Safecast/bGeigieNanoKit/hardware/bGeigieNanoKit v1.0r4/bGeigieNanoKit v1.0r4_board.png

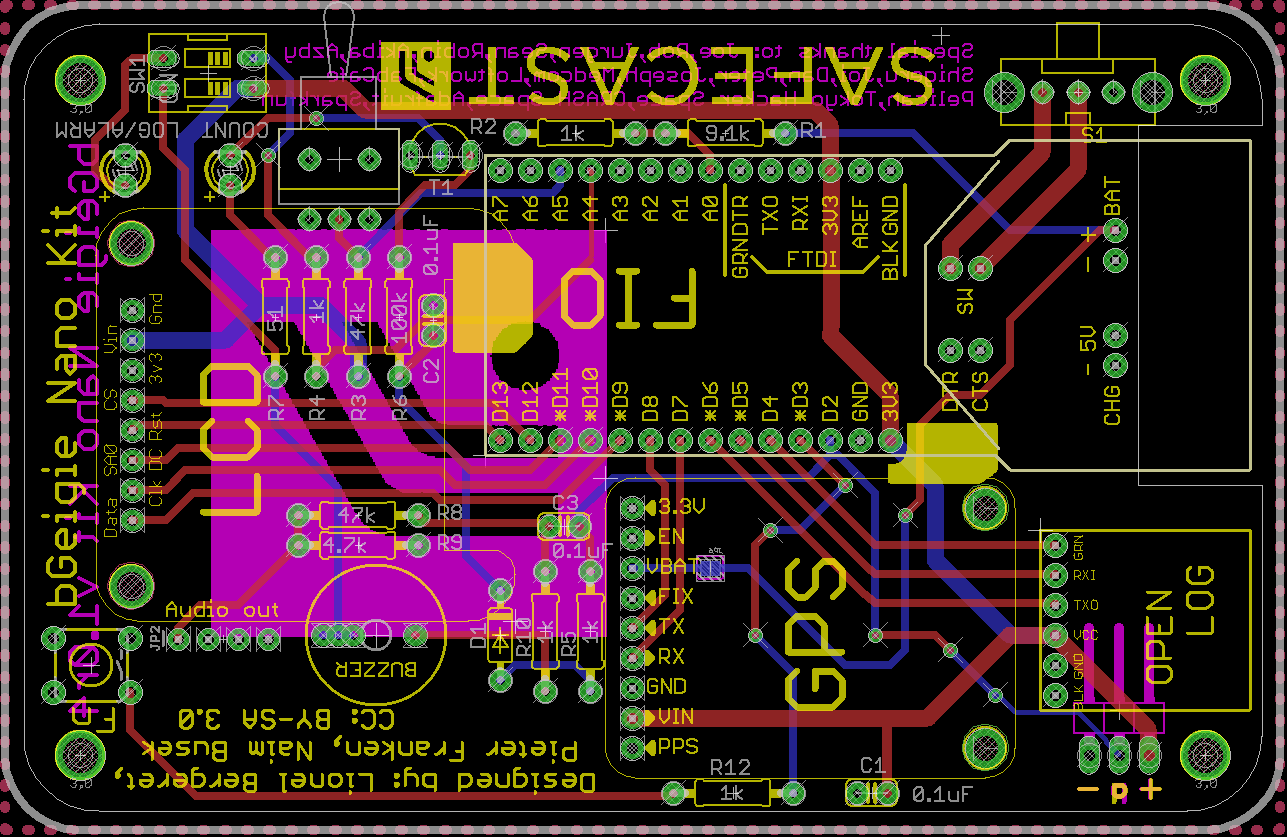
hardware/bGeigieNanoKit v1.0r4/bGeigieNanoKit v1.0r4_board.png
