Safecast/bGeigieNanoKit/hardware/bGeigieNanoKit V1.1r5/2017-06-08_bGeigieNanoKit V1.1r5x/bGeigieNano_V1.15x_board.jpg

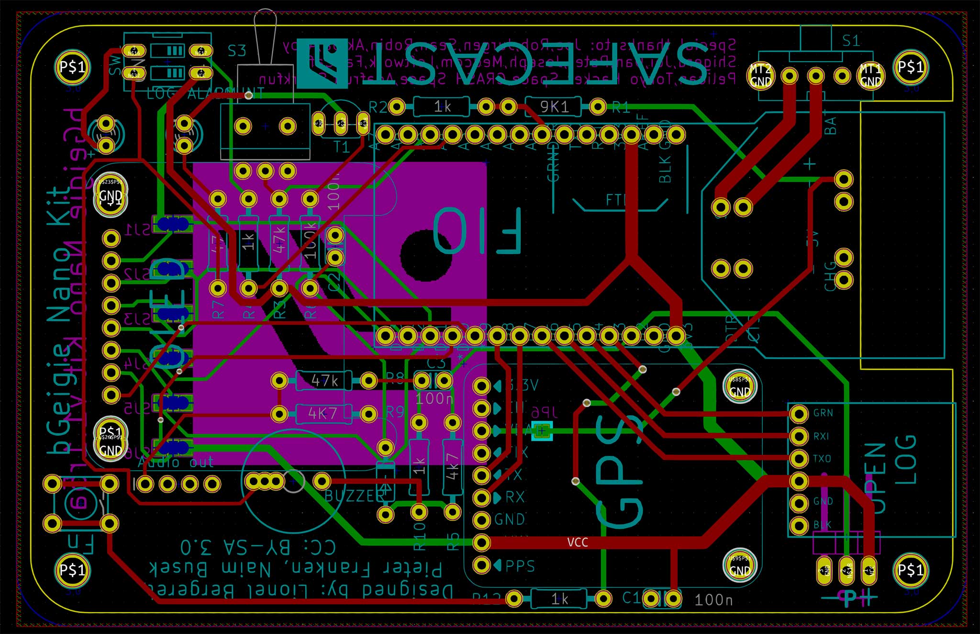
hardware/bGeigieNanoKit V1.1r5/2017-06-08_bGeigieNanoKit V1.1r5x/bGeigieNano_V1.15x_board.jpg
