Safecast/bGeigieNanoKit/hardware/bGeigieNanoKit/board_v1.1r4x.png

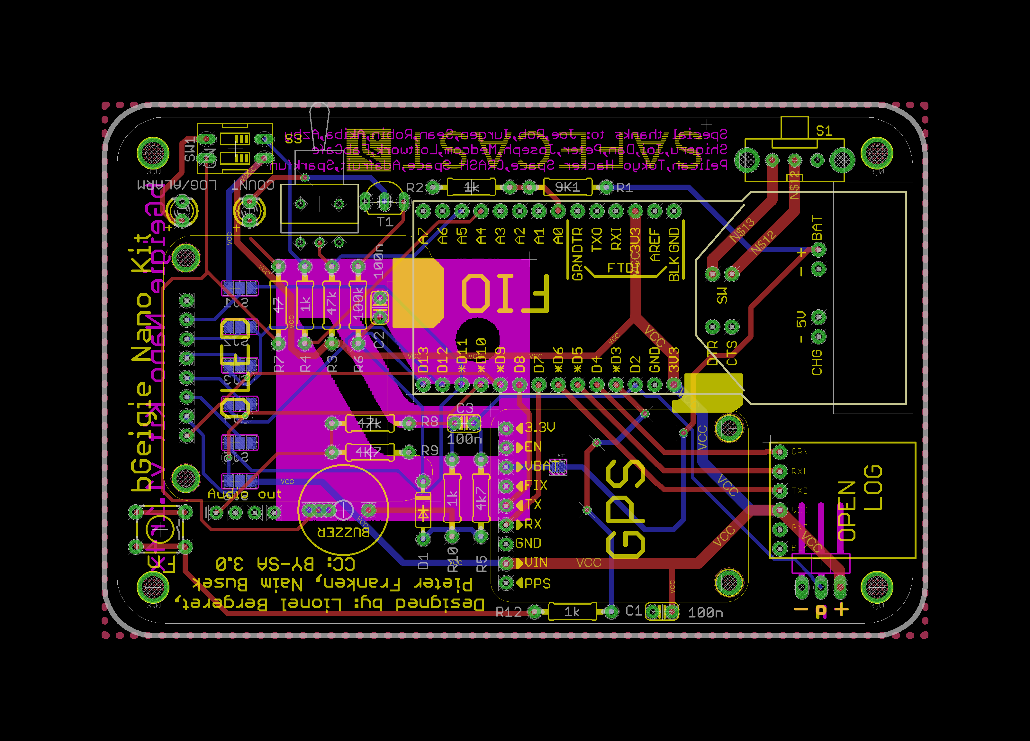
hardware/bGeigieNanoKit/board_v1.1r4x.png
