Safecast/bGeigieNanoKit/hardware/bGeigieNanoKit/S2660001.JPG

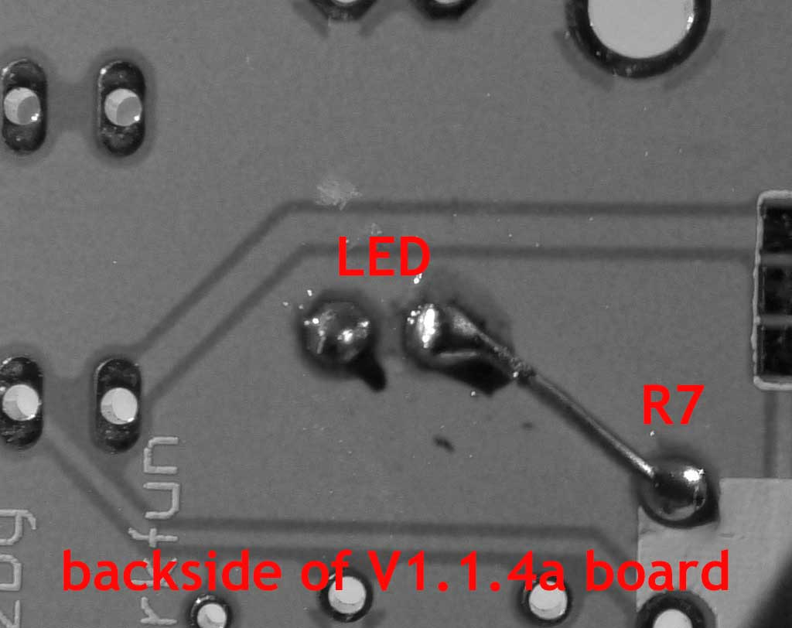
hardware/bGeigieNanoKit/S2660001.JPG
