Safecast/bGeigieNanoKit/nano manual named pics/manual update Aug 2018 small JPEG selects/078 wiki_small_components_31000px.jpg

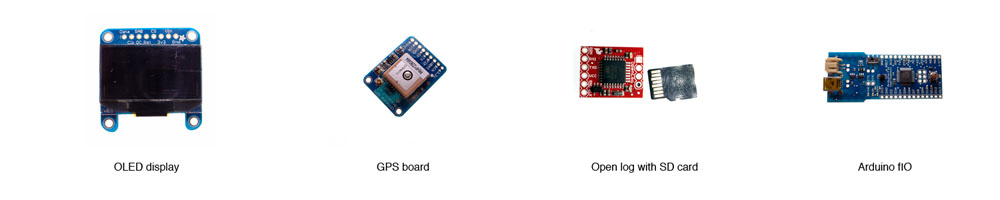
nano manual named pics/manual update Aug 2018 small JPEG selects/078 wiki_small_components_31000px.jpg
