Safecast/bGeigieNanoKit/nano manual named pics/manual update Aug 2018 small JPEG selects/_020-SmallComponentsIn-1000px[new].jpg

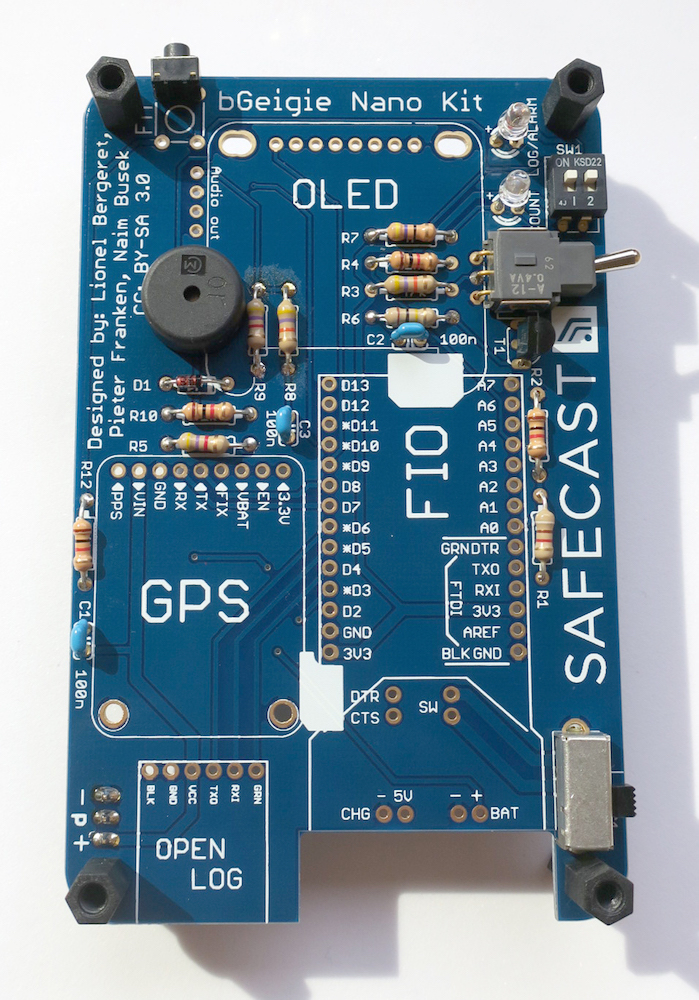
nano manual named pics/manual update Aug 2018 small JPEG selects/_020-SmallComponentsIn-1000px[new].jpg
