Safecast/bGeigieNanoKit/nano manual named pics/manual update Aug 2018 small JPEG selects/v1.0r3_placement guide large parts.jpg

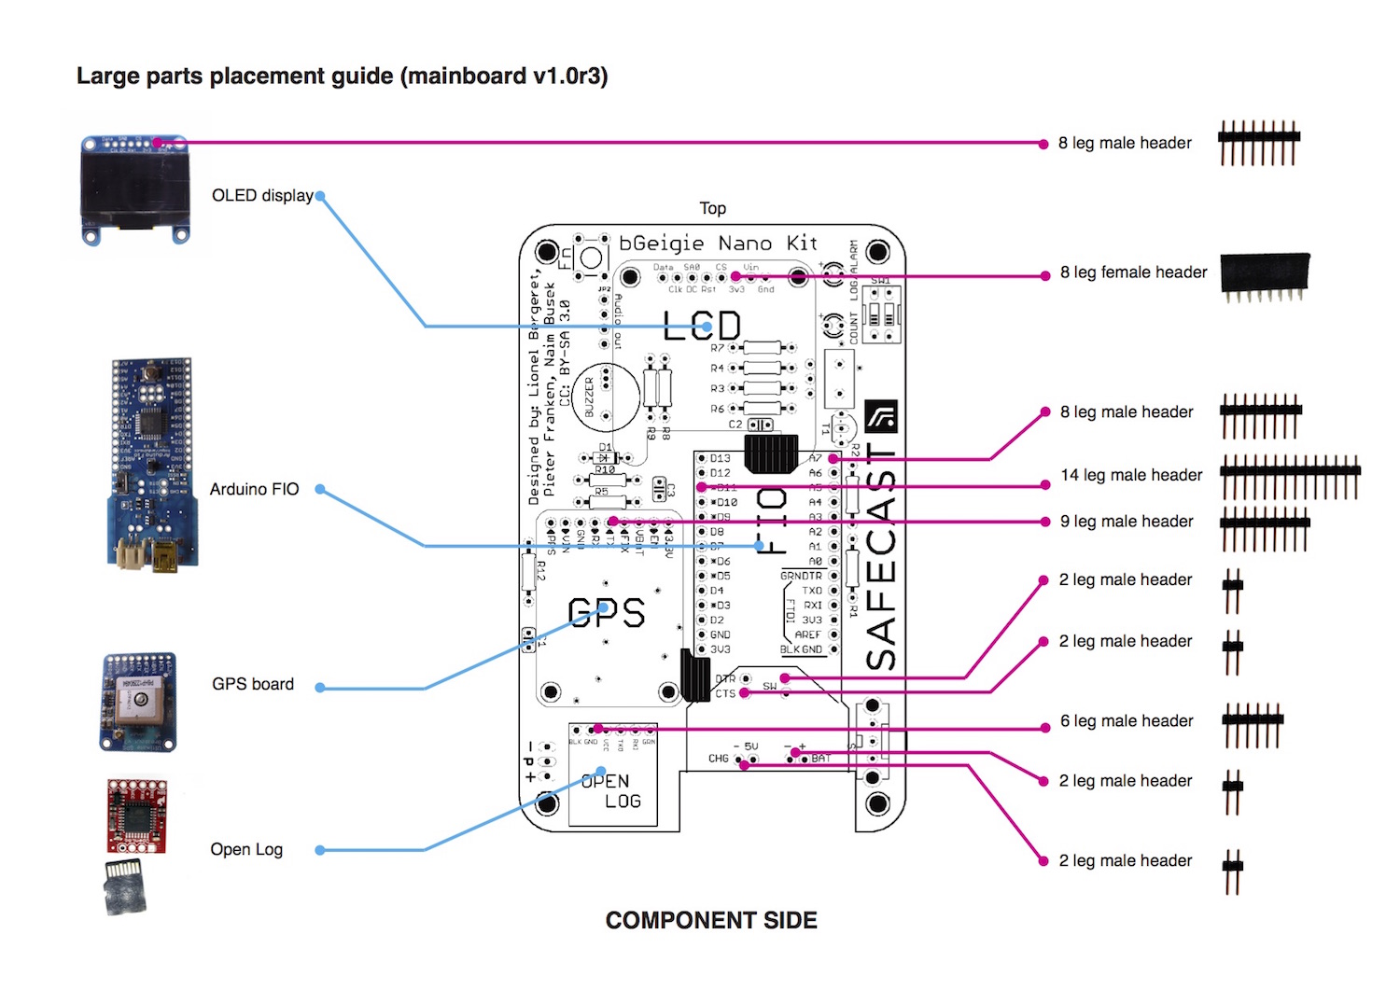
nano manual named pics/manual update Aug 2018 small JPEG selects/v1.0r3_placement guide large parts.jpg
