Safecast/bGeigieNanoKit/nano manual named pics/wiki_small_components_2.jpg

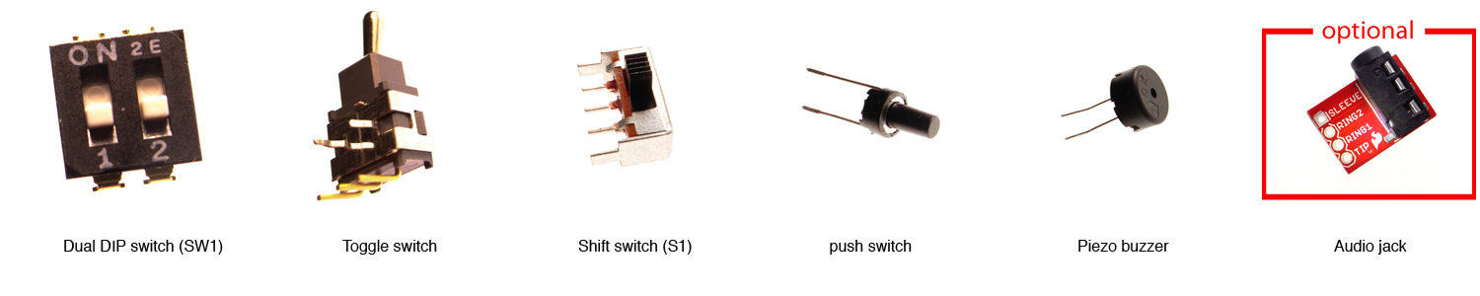
nano manual named pics/wiki_small_components_2.jpg
