Safecast/bGeigieNanoKit/nano manual named pics/wiki_small_components_4.jpg

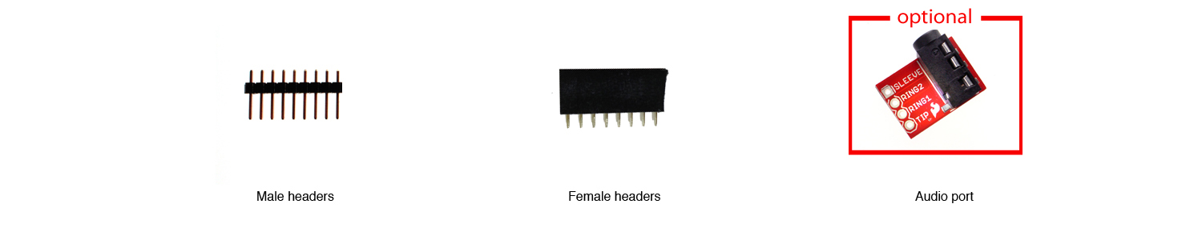
nano manual named pics/wiki_small_components_4.jpg
