Safecast/bGeigieNanoKit/assembly/bGeigieNanoKit_bb.png

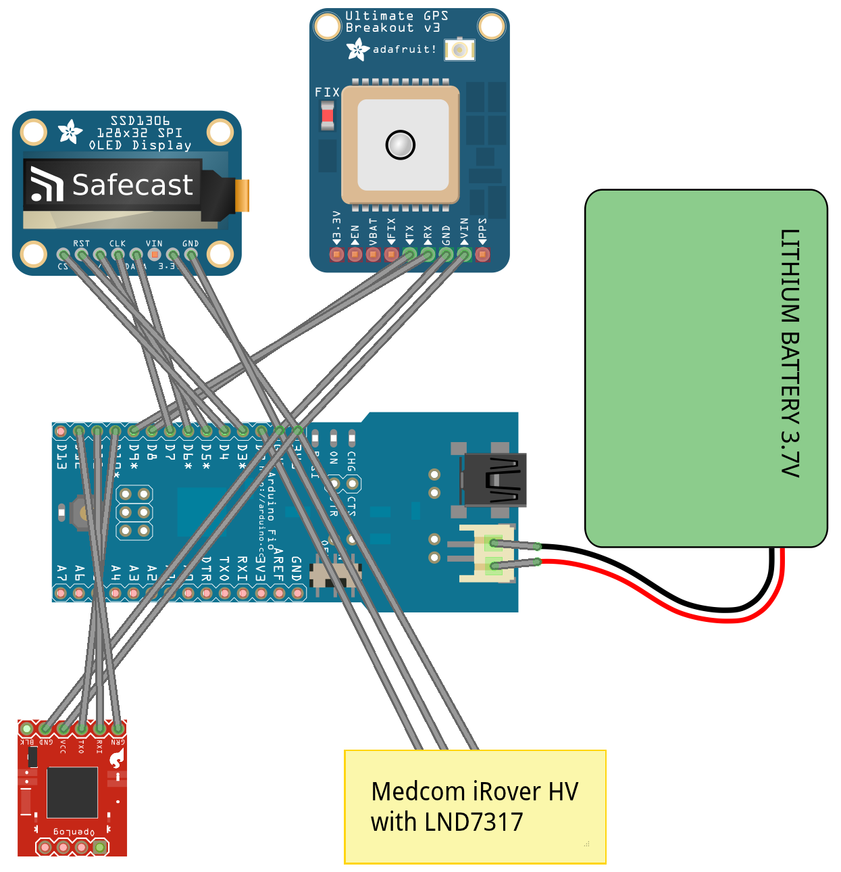
assembly/bGeigieNanoKit_bb.png
