Safecast/bGeigieNanoKit/assembly/bGeigieNanoKit_sheet.png

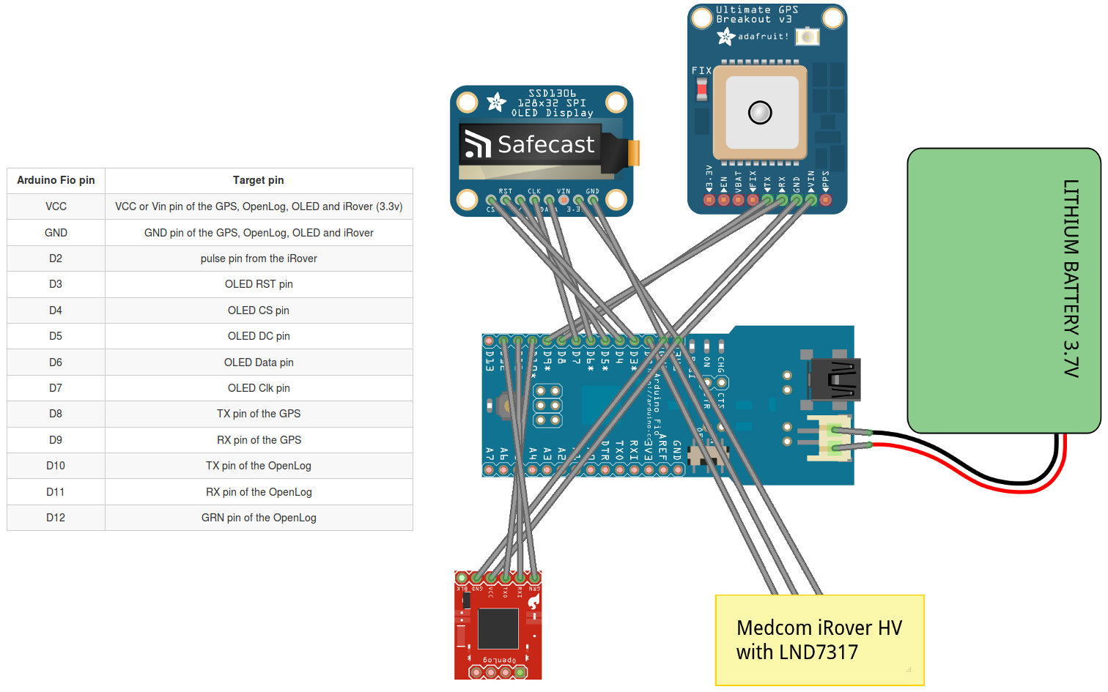
assembly/bGeigieNanoKit_sheet.png
