Safecast/bGeigieNanoKit/nano manual named pics/assembly.jpg

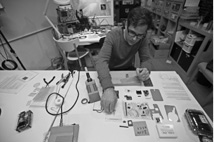
nano manual named pics/assembly.jpg
