Safecast/bGeigieNanoKit/nano manual named pics/attaching_iRover.jpg

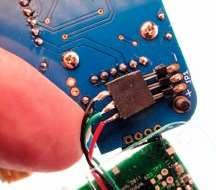
nano manual named pics/attaching_iRover.jpg
