Safecast/bGeigieNanoKit/nano manual named pics/attaching_sensor_to_iRover.jpg

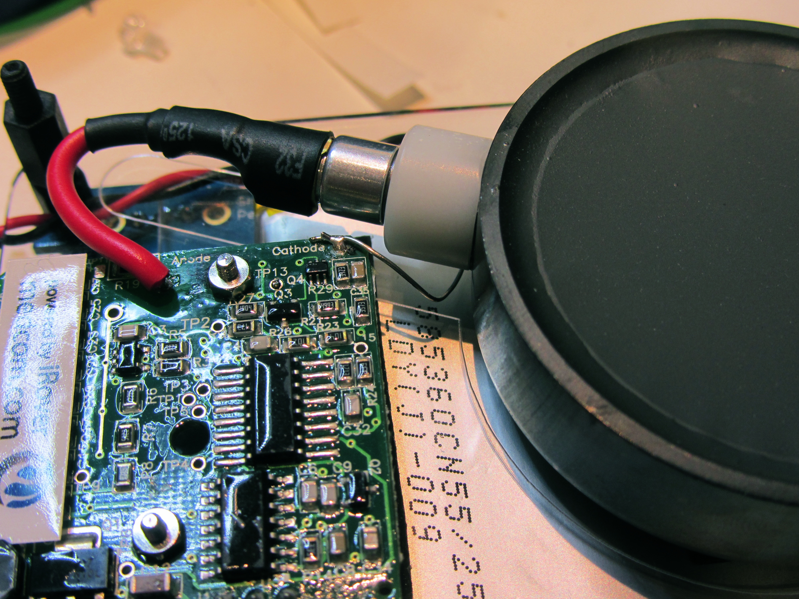
nano manual named pics/attaching_sensor_to_iRover.jpg
