Safecast/bGeigieNanoKit/nano manual named pics/back_headers_top.jpg

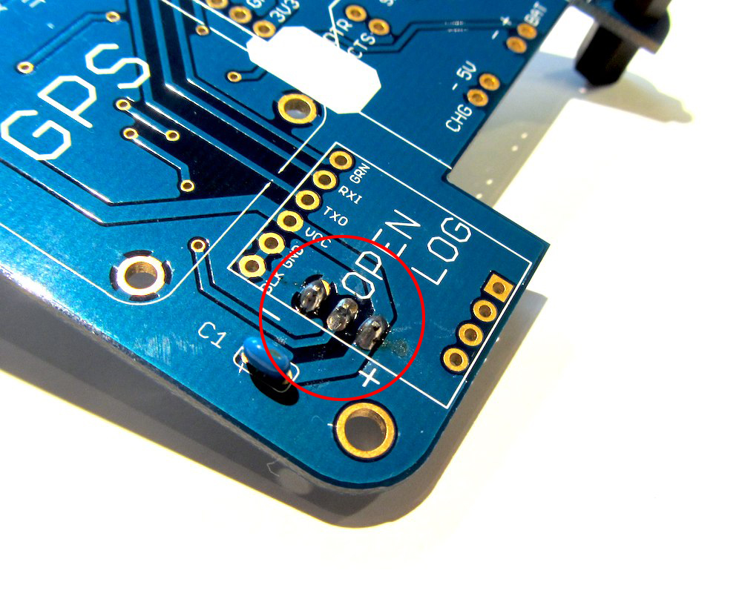
nano manual named pics/back_headers_top.jpg
