Safecast/bGeigieNanoKit/nano manual named pics/back_plate_install.jpg

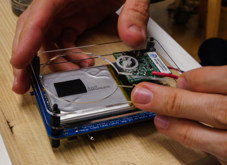
nano manual named pics/back_plate_install.jpg
