Safecast/bGeigieNanoKit/nano manual named pics/battery-compo01.jpg

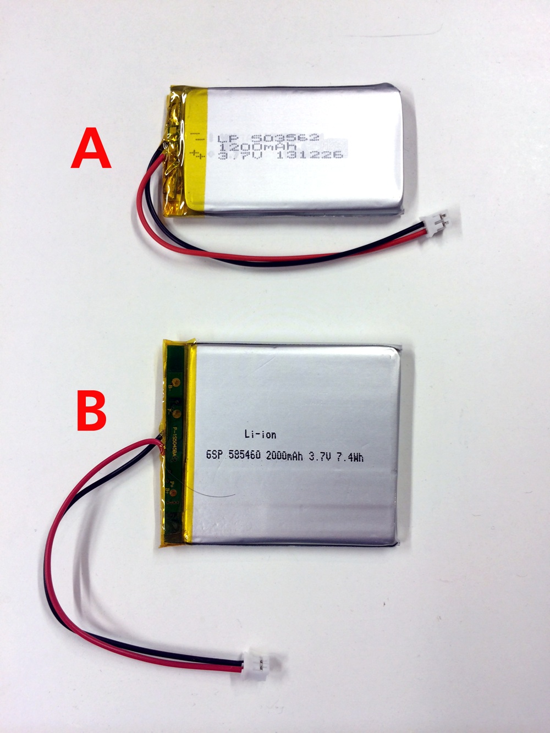
nano manual named pics/battery-compo01.jpg
