Safecast/bGeigieNanoKit/nano manual named pics/battery_location.jpg

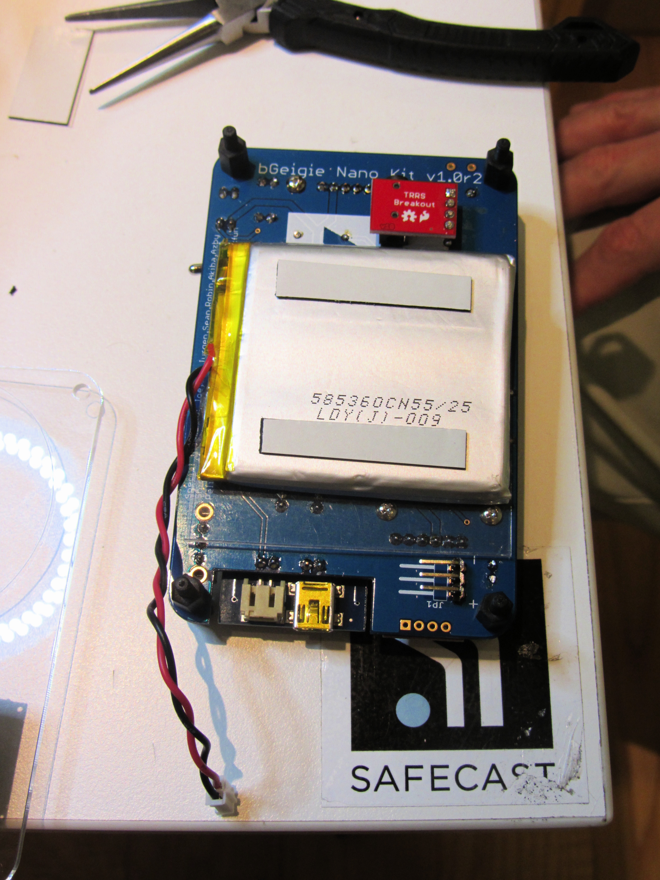
nano manual named pics/battery_location.jpg
