Safecast/bGeigieNanoKit/nano manual named pics/beercantrick.jpg

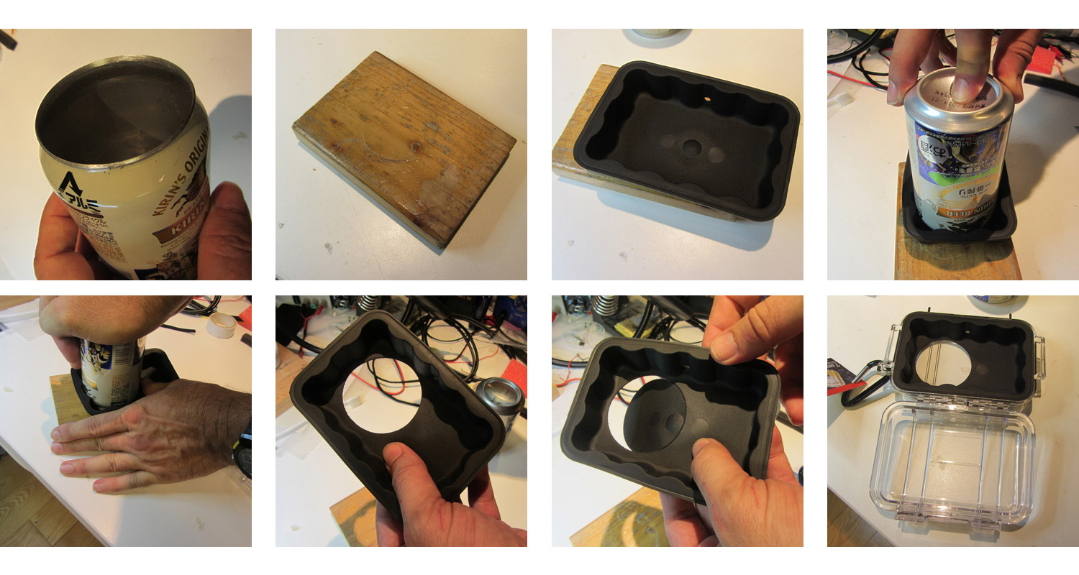
nano manual named pics/beercantrick.jpg
