Safecast/bGeigieNanoKit/nano manual named pics/bGeigie_Nano_bottom.jpg

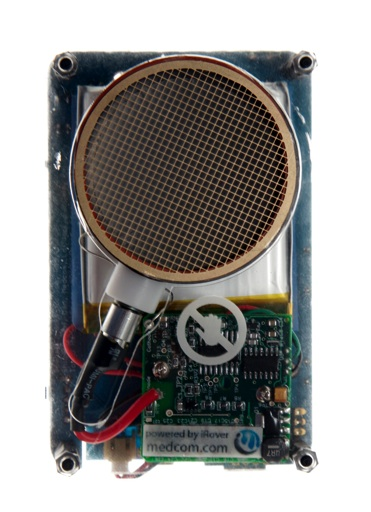
nano manual named pics/bGeigie_Nano_bottom.jpg
