Safecast/bGeigieNanoKit/nano manual named pics/bGeigie_Nano_side2.jpg

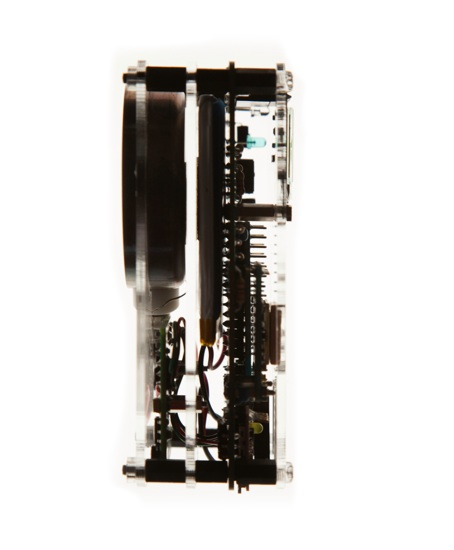
nano manual named pics/bGeigie_Nano_side2.jpg
