Safecast/bGeigieNanoKit/nano manual named pics/bGeigie_Nano_side.jpg

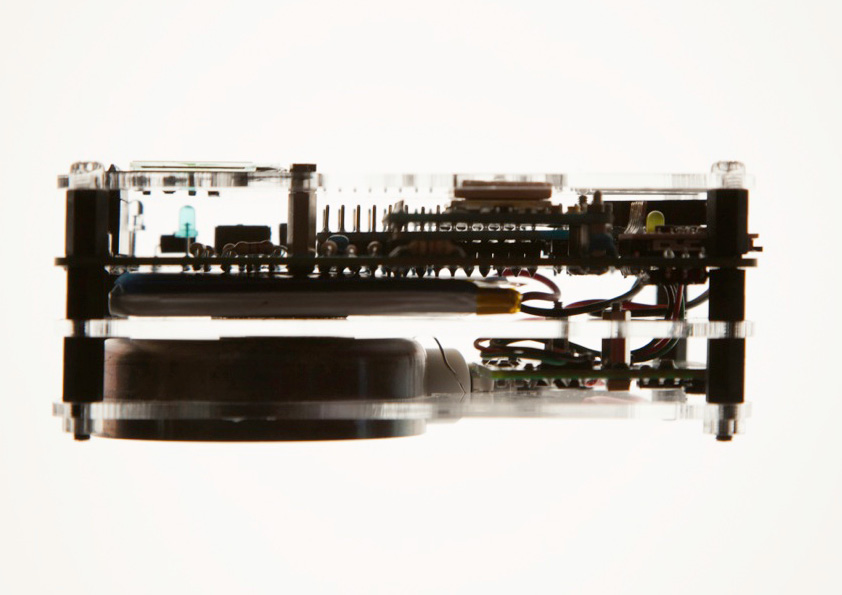
nano manual named pics/bGeigie_Nano_side.jpg
