Safecast/bGeigieNanoKit/nano manual named pics/broken_sensor.jpg

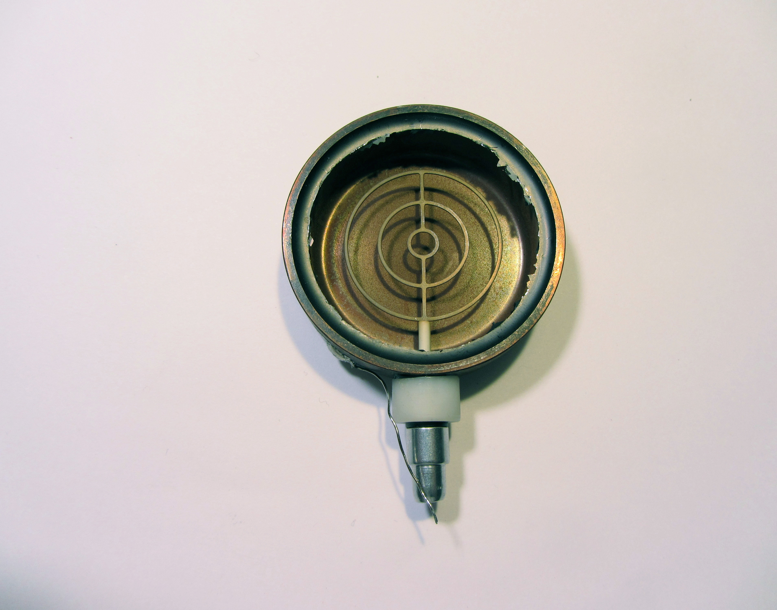
nano manual named pics/broken_sensor.jpg
