Safecast/bGeigieNanoKit/nano manual named pics/buttonguideNano.jpg

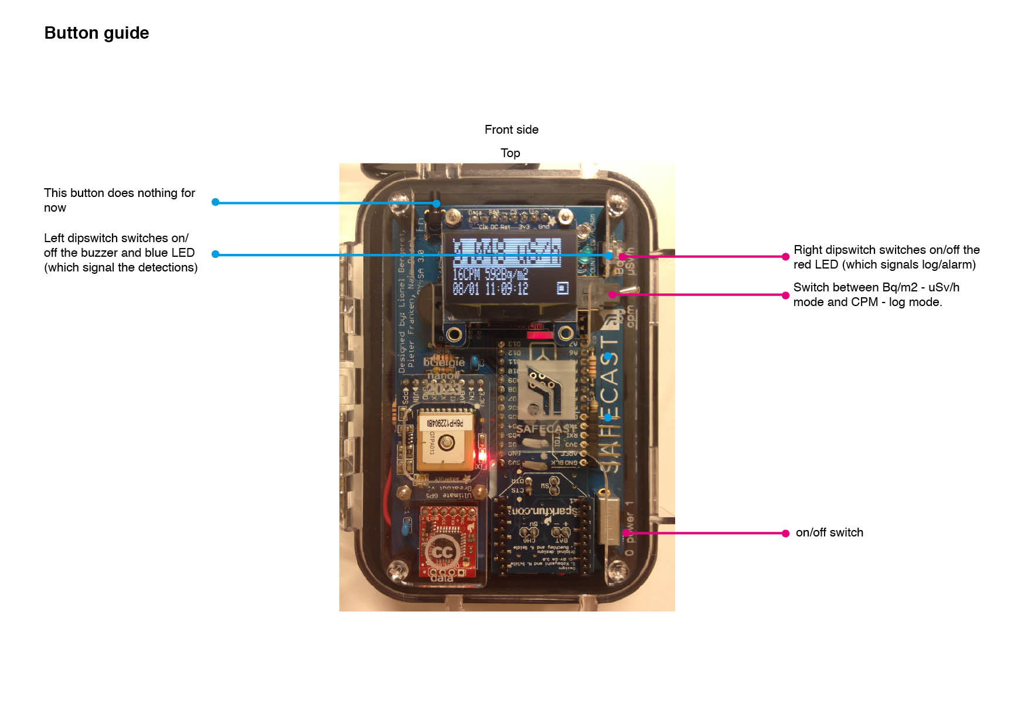
nano manual named pics/buttonguideNano.jpg
