Safecast/bGeigieNanoKit/nano manual named pics/closed_front.jpg

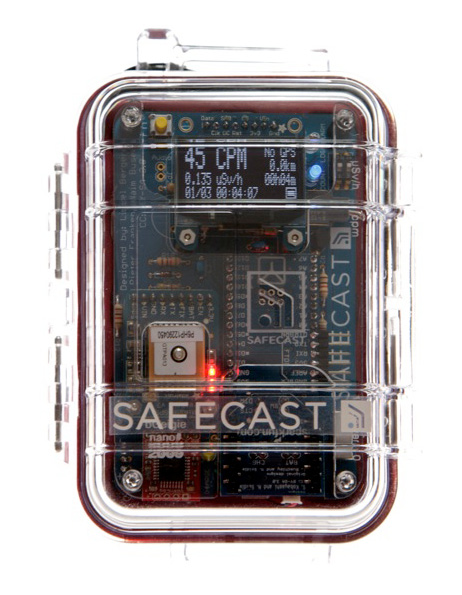
nano manual named pics/closed_front.jpg
