Safecast/bGeigieNanoKit/nano manual named pics/cutting_liner.jpg

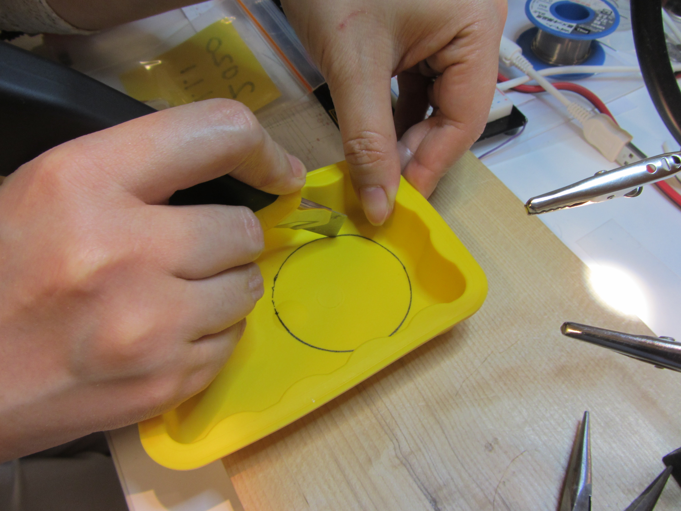
nano manual named pics/cutting_liner.jpg
