Safecast/bGeigieNanoKit/nano manual named pics/displayupdate/2020-new-display-cut-jumper.jpg

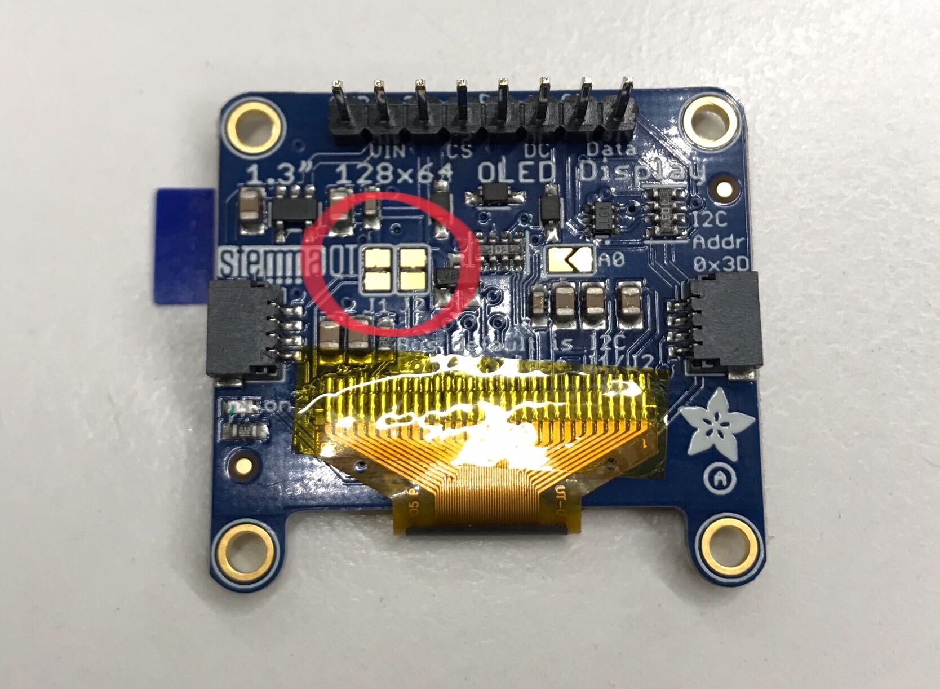
nano manual named pics/displayupdate/2020-new-display-cut-jumper.jpg
