Safecast/bGeigieNanoKit/nano manual named pics/displayupdate/2020-new-display-post-cut.jpg

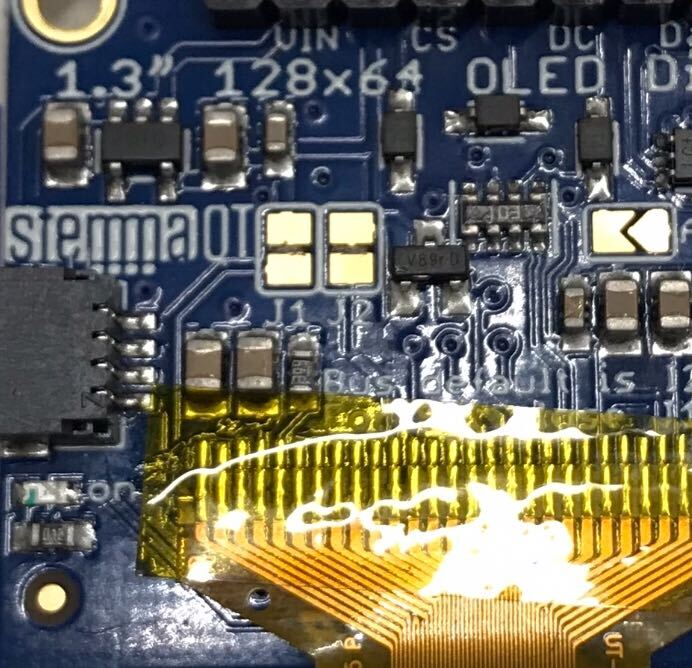
nano manual named pics/displayupdate/2020-new-display-post-cut.jpg
