Safecast/bGeigieNanoKit/nano manual named pics/displayupdate/2020-new-display-pre-cut.jpg

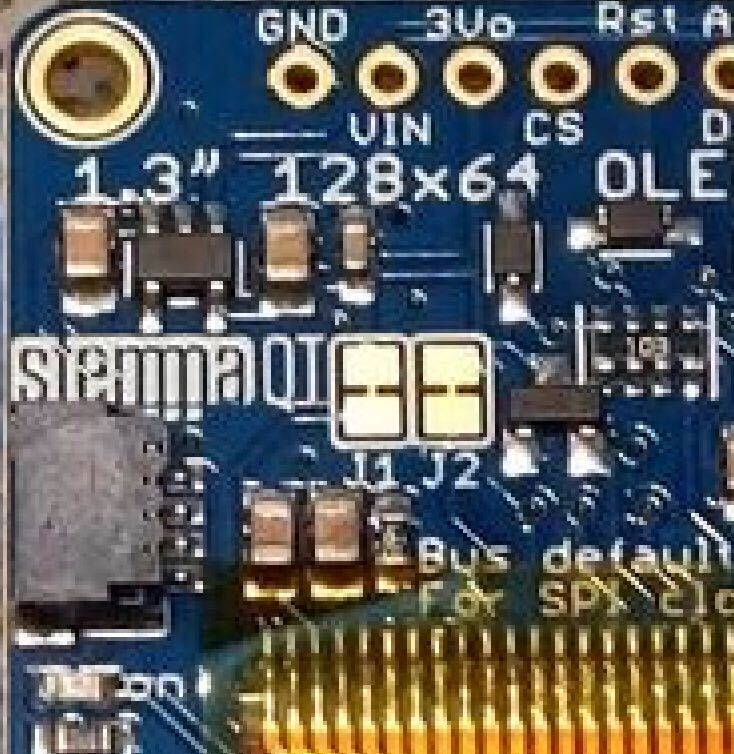
nano manual named pics/displayupdate/2020-new-display-pre-cut.jpg
