Safecast/bGeigieNanoKit/nano manual named pics/finished_assembly_top.jpg

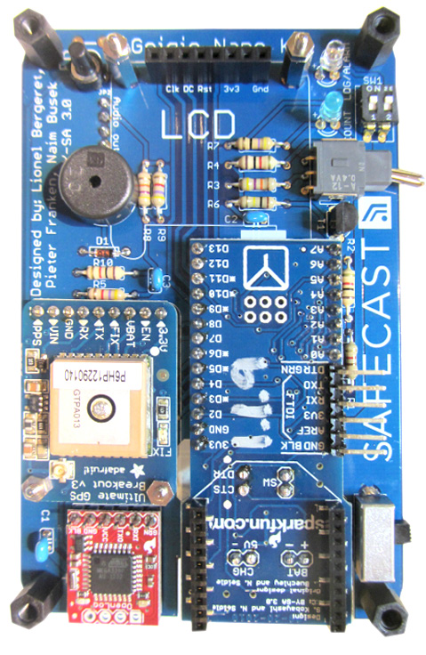
nano manual named pics/finished_assembly_top.jpg
