Safecast/bGeigieNanoKit/nano manual named pics/Fio_header_tip2.jpg

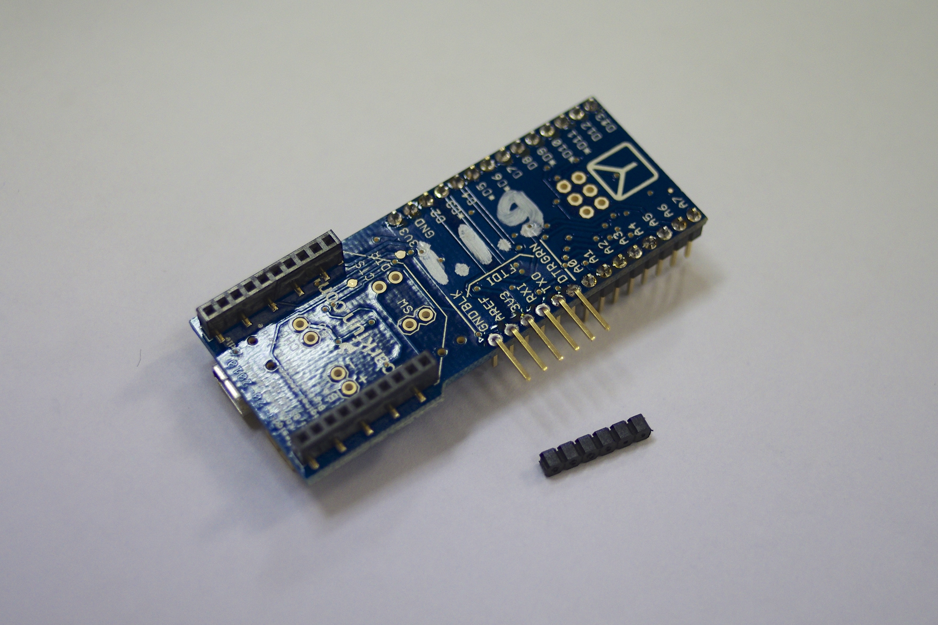
nano manual named pics/Fio_header_tip2.jpg
