Safecast/bGeigieNanoKit/nano manual named pics/Fio_header_tip.jpg

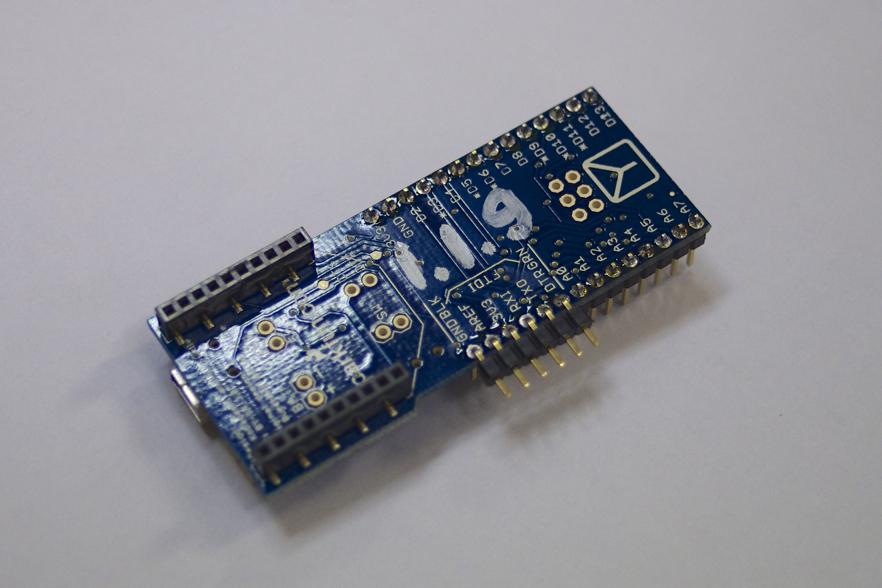
nano manual named pics/Fio_header_tip.jpg
