Safecast/bGeigieNanoKit/nano manual named pics/fio_placement.jpg

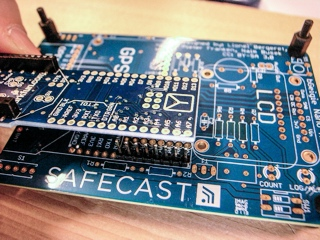
nano manual named pics/fio_placement.jpg
