Safecast/bGeigieNanoKit/nano manual named pics/fully_assembled_top.jpg

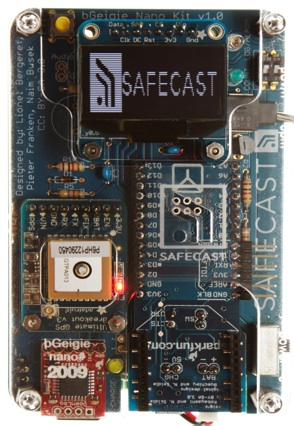
nano manual named pics/fully_assembled_top.jpg
