Safecast/bGeigieNanoKit/nano manual named pics/gps_placement.jpg

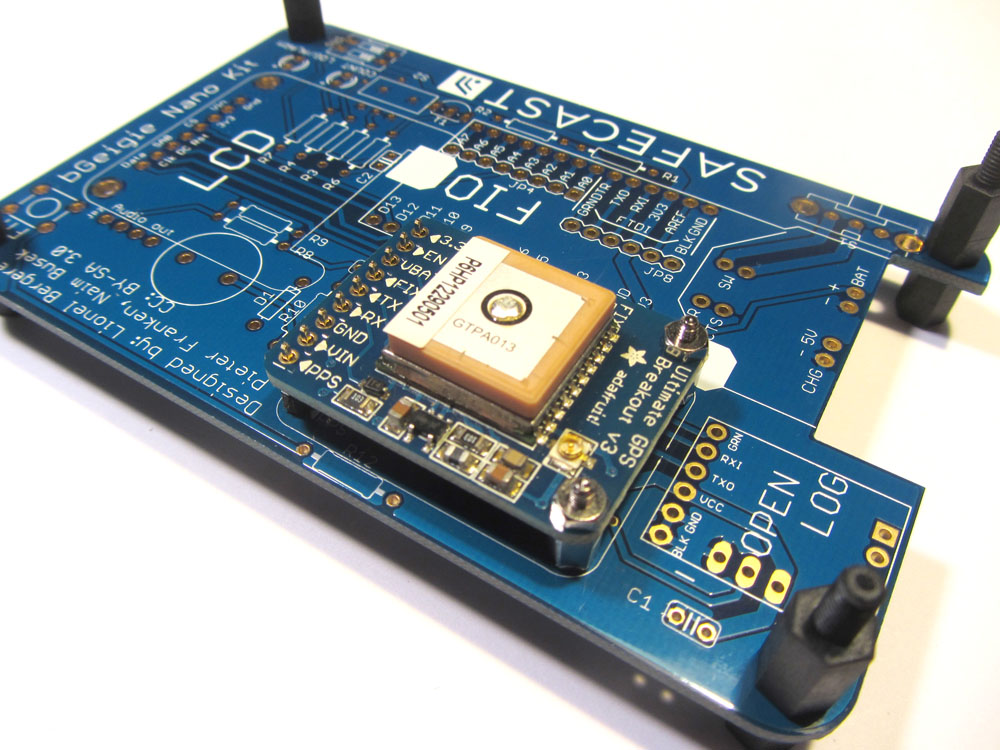
nano manual named pics/gps_placement.jpg
