Safecast/bGeigieNanoKit/nano manual named pics/iRover_attachment.jpg

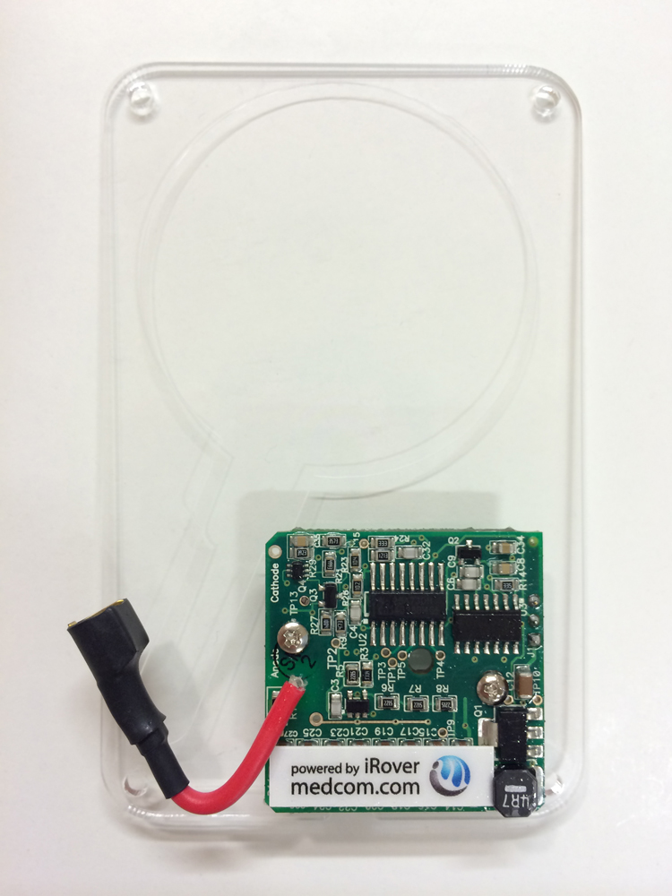
nano manual named pics/iRover_attachment.jpg
