Safecast/bGeigieNanoKit/nano manual named pics/iRover_header_tip2.jpg

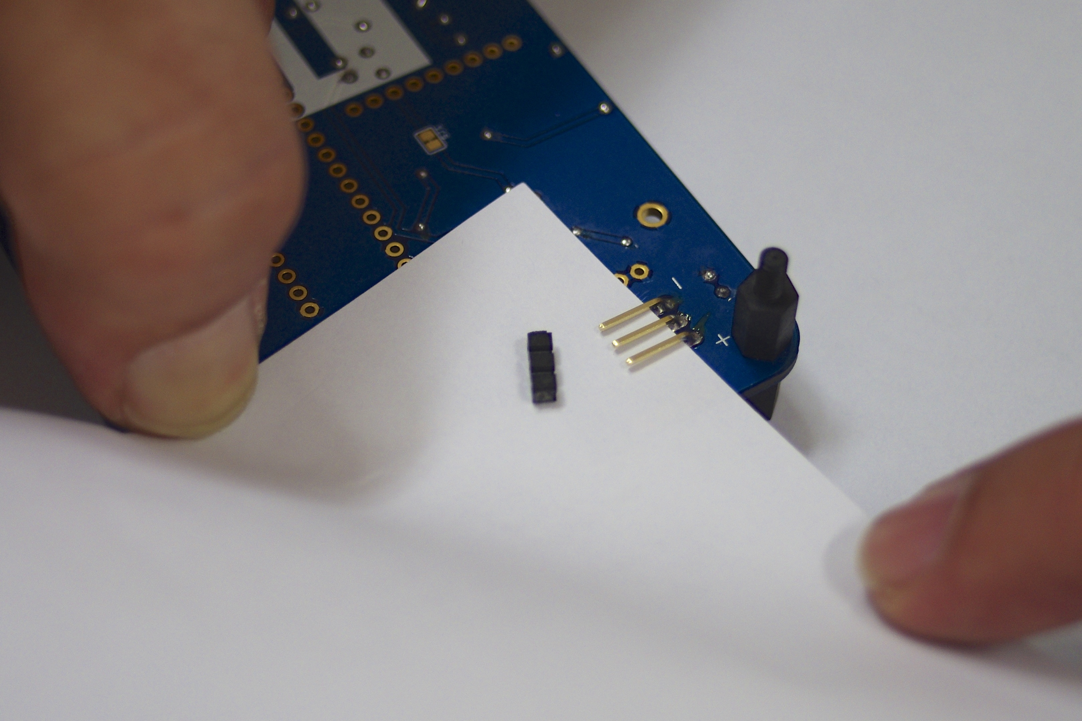
nano manual named pics/iRover_header_tip2.jpg
