Safecast/bGeigieNanoKit/nano manual named pics/iRover_headers.jpg

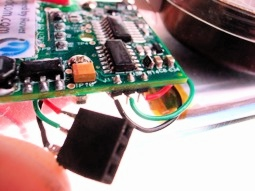
nano manual named pics/iRover_headers.jpg
