Safecast/bGeigieNanoKit/nano manual named pics/iRover_placement.jpg

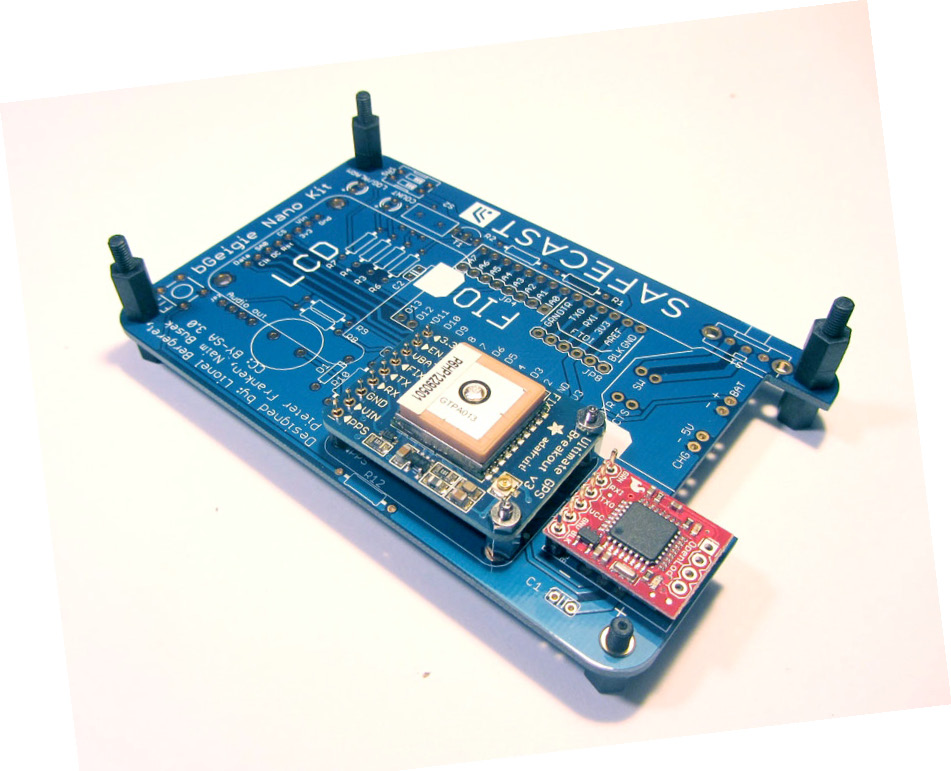
nano manual named pics/iRover_placement.jpg
