Safecast/bGeigieNanoKit/nano manual named pics/iRover_positioning.jpg

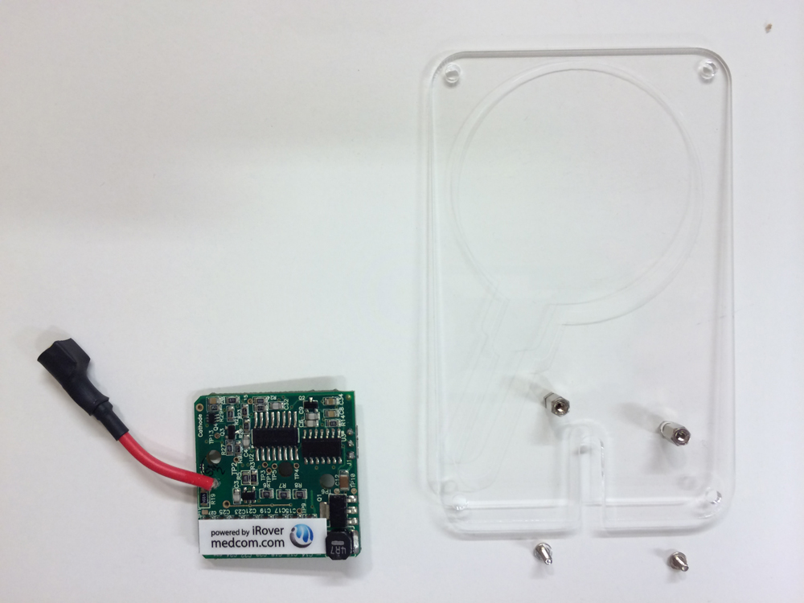
nano manual named pics/iRover_positioning.jpg
