Safecast/bGeigieNanoKit/nano manual named pics/iRover_wire_feedthrough.jpg

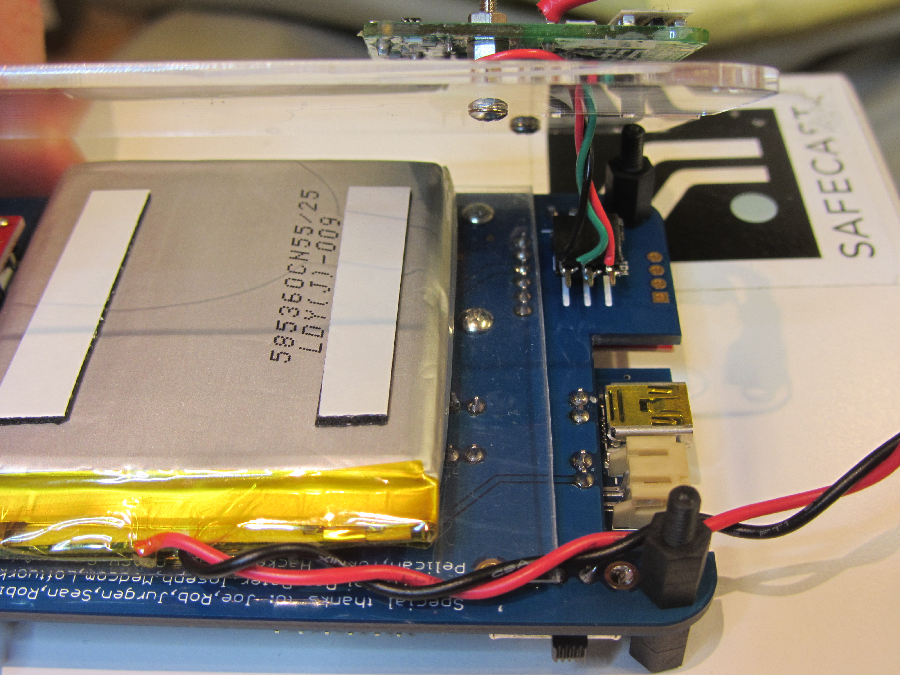
nano manual named pics/iRover_wire_feedthrough.jpg
