Safecast/bGeigieNanoKit/nano manual named pics/iRover_wiring.jpg

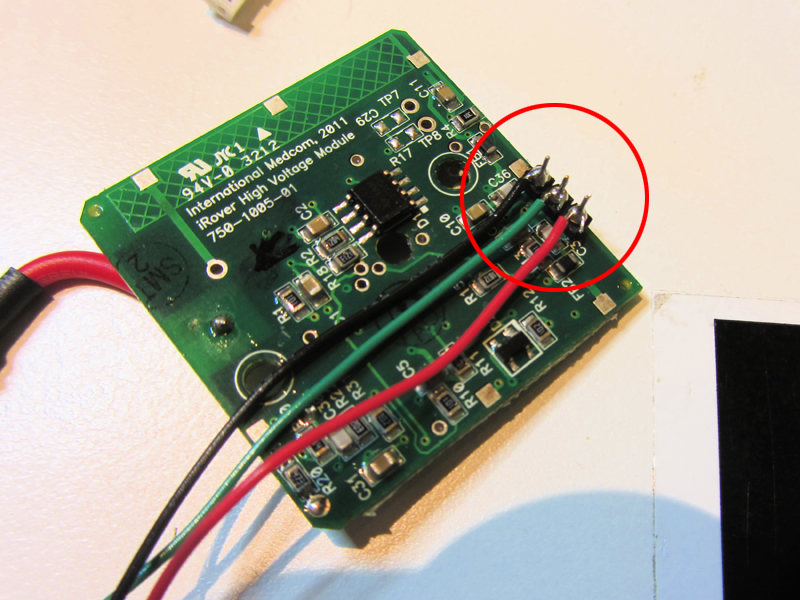
nano manual named pics/iRover_wiring.jpg
