Safecast/bGeigieNanoKit/nano manual named pics/lcd_header_placement.jpg

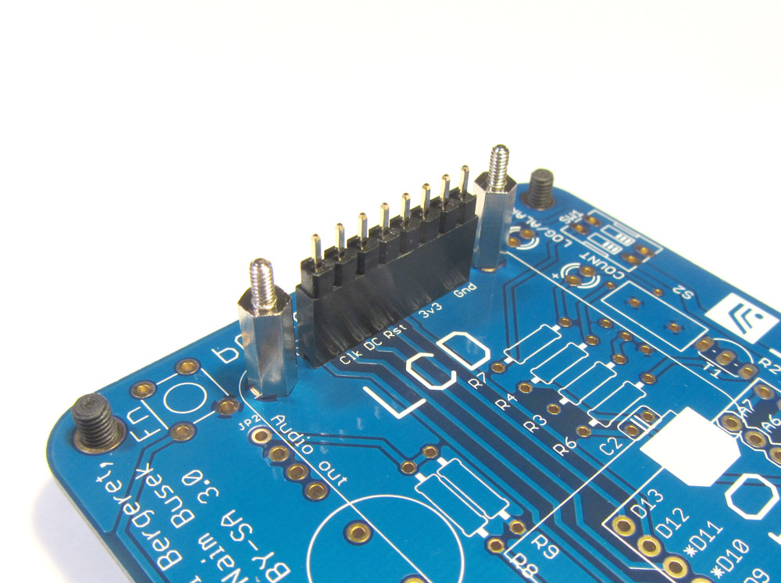
nano manual named pics/lcd_header_placement.jpg
