Safecast/bGeigieNanoKit/nano manual named pics/lcd_placement_top.jpg

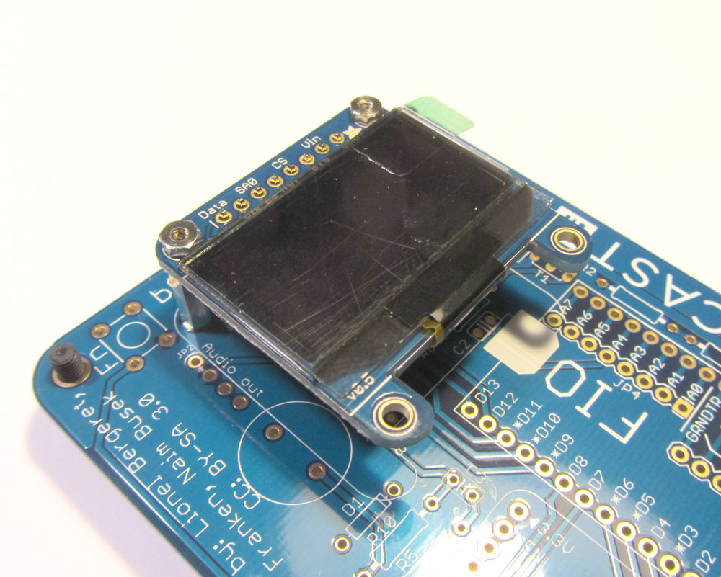
nano manual named pics/lcd_placement_top.jpg
