Safecast/bGeigieNanoKit/nano manual named pics/manual update Aug 2018 small JPEG selects/01- Nano 01b-800px[new].jpg

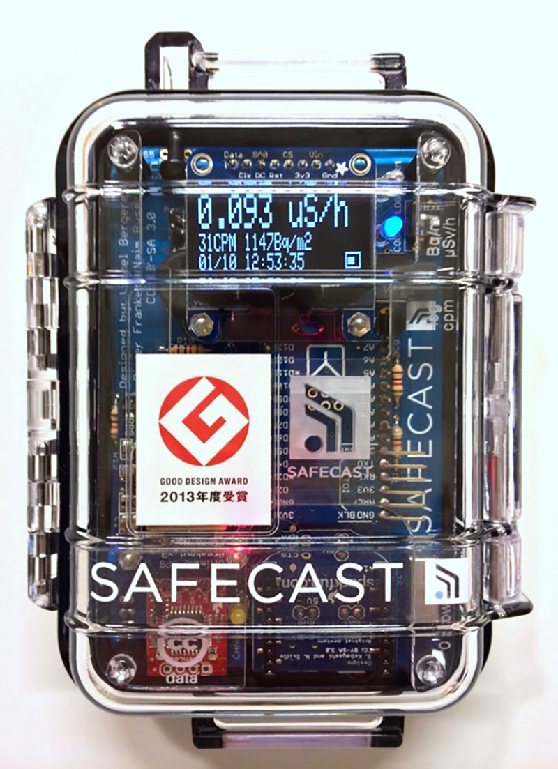
nano manual named pics/manual update Aug 2018 small JPEG selects/01- Nano 01b-800px[new].jpg
