Safecast/bGeigieNanoKit/nano manual named pics/manual update Aug 2018 small JPEG selects/001-MainBoardFront1000px[new].jpg

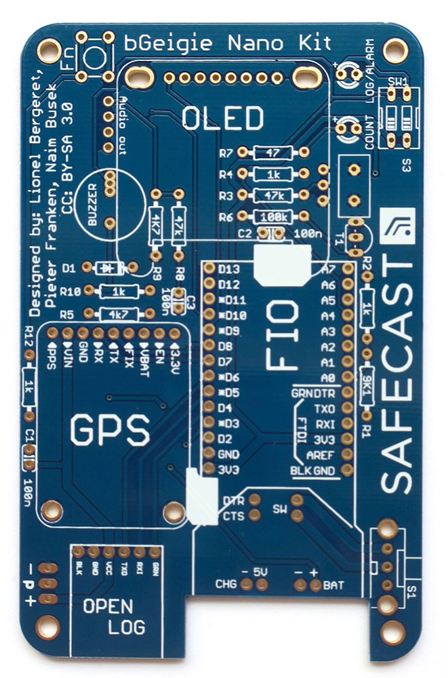
nano manual named pics/manual update Aug 2018 small JPEG selects/001-MainBoardFront1000px[new].jpg
