Safecast/bGeigieNanoKit/nano manual named pics/manual update Aug 2018 small JPEG selects/1.1r5x_smallcomponentsV01.jpg

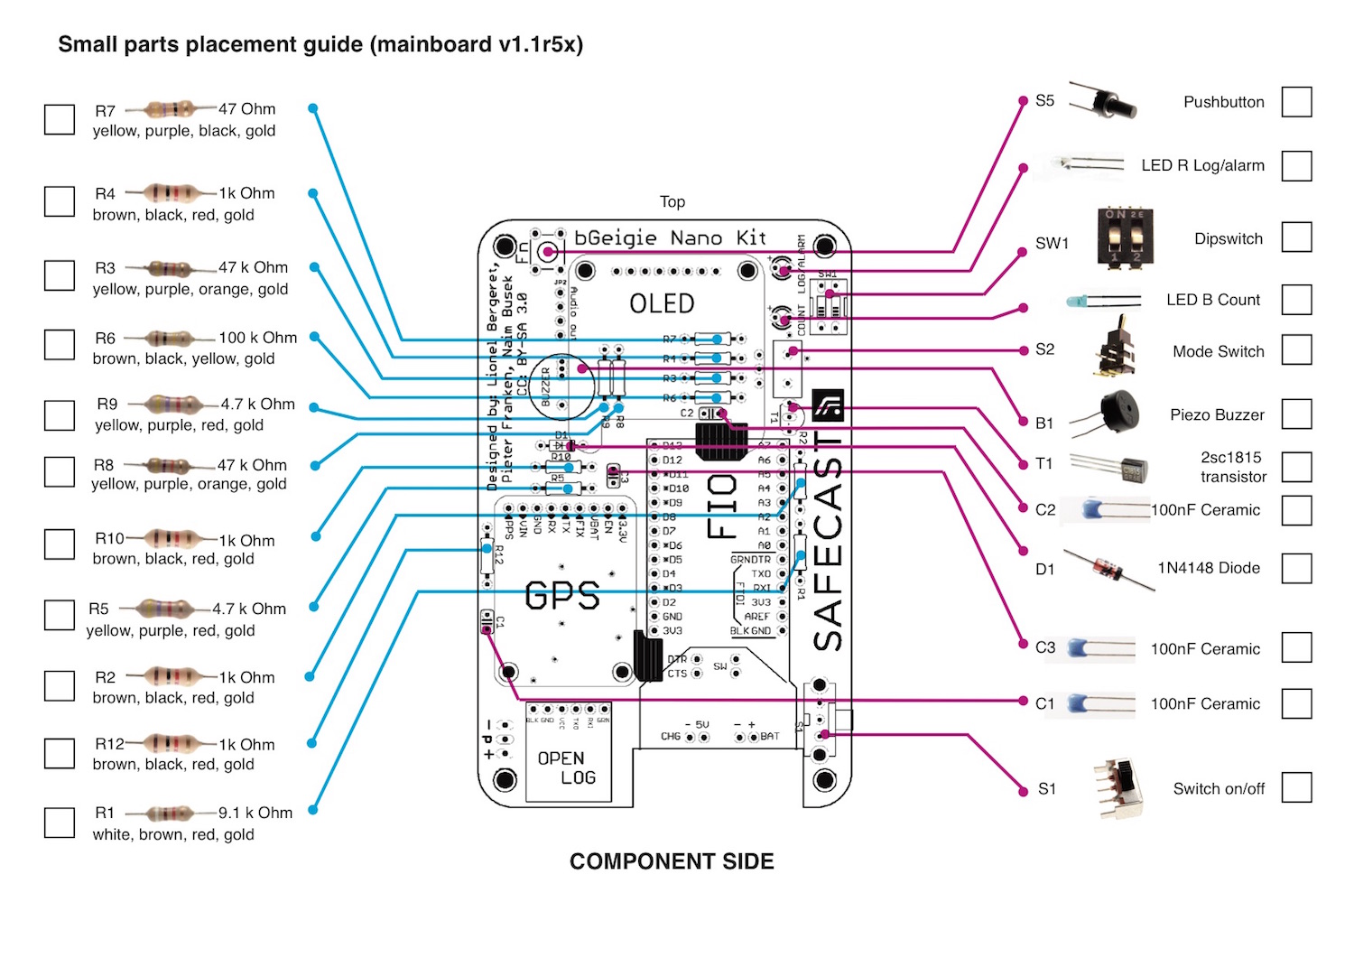
nano manual named pics/manual update Aug 2018 small JPEG selects/1.1r5x_smallcomponentsV01.jpg
