Safecast/bGeigieNanoKit/nano manual named pics/manual update Aug 2018 small JPEG selects/010-LED-RedBlue1000pxAnnotated.jpg

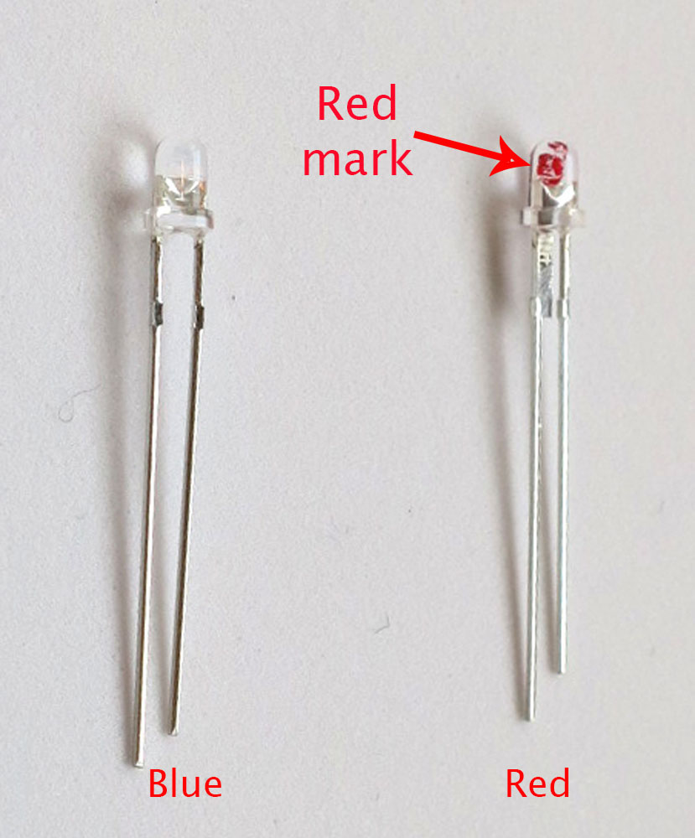
nano manual named pics/manual update Aug 2018 small JPEG selects/010-LED-RedBlue1000pxAnnotated.jpg
