Safecast/bGeigieNanoKit/nano manual named pics/manual update Aug 2018 small JPEG selects/013-TransistorInstalled1000pxAnnotated.jpg

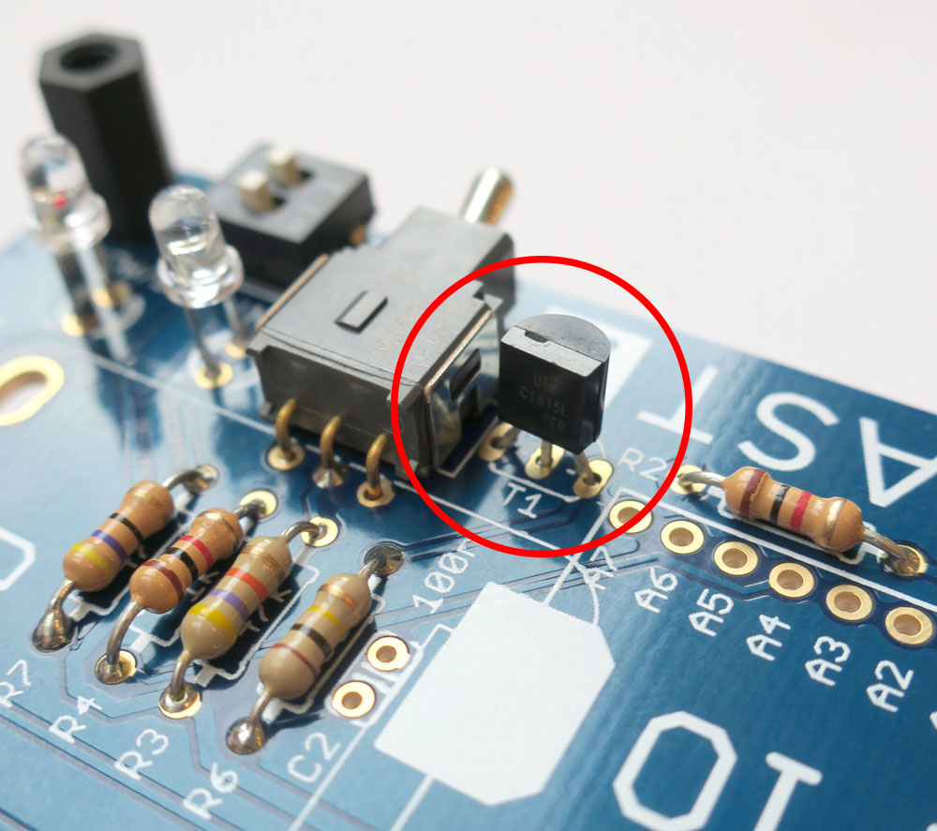
nano manual named pics/manual update Aug 2018 small JPEG selects/013-TransistorInstalled1000pxAnnotated.jpg
