Safecast/bGeigieNanoKit/nano manual named pics/manual update Aug 2018 small JPEG selects/016-TripleConnectorWithLead1000pxAnnotated.jpg

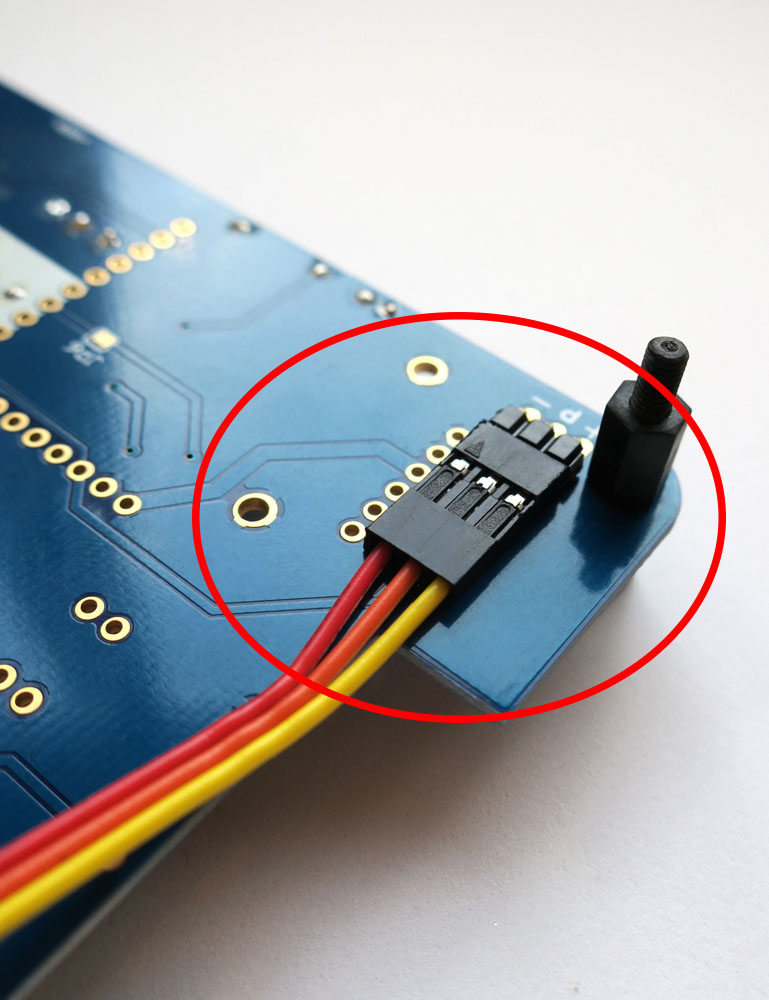
nano manual named pics/manual update Aug 2018 small JPEG selects/016-TripleConnectorWithLead1000pxAnnotated.jpg
