Safecast/bGeigieNanoKit/nano manual named pics/manual update Aug 2018 small JPEG selects/017 TripleConnectorInPlace1000pxAnnotated.jpg

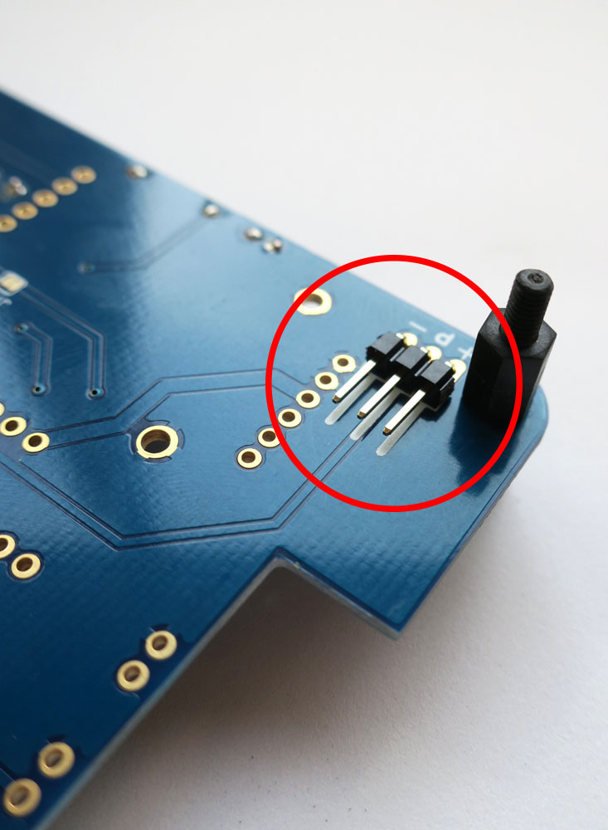
nano manual named pics/manual update Aug 2018 small JPEG selects/017 TripleConnectorInPlace1000pxAnnotated.jpg
