Safecast/bGeigieNanoKit/nano manual named pics/manual update Aug 2018 small JPEG selects/018-TripleConnectorSolder011000pxAnnotated.jpg

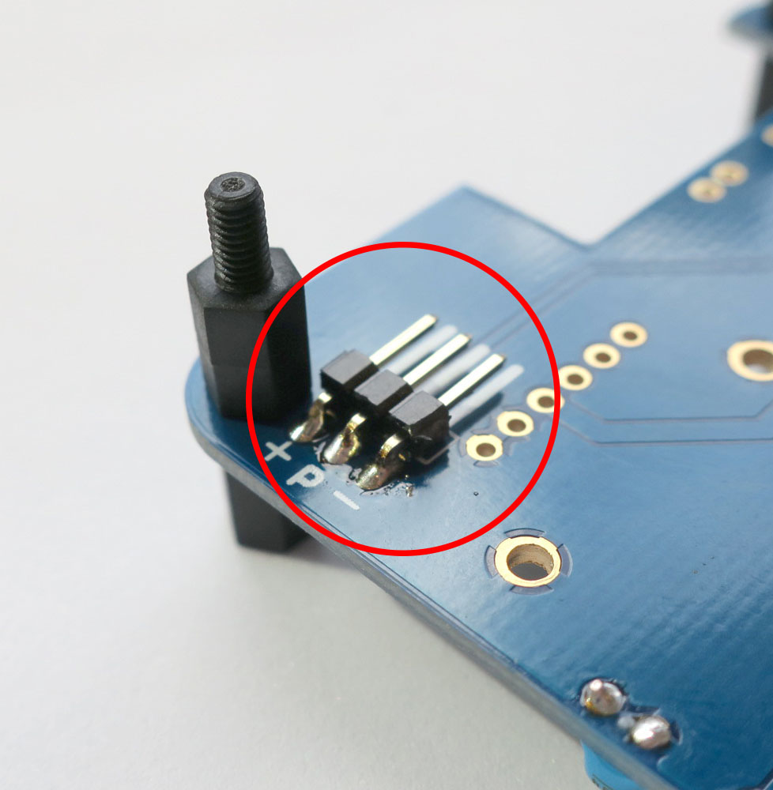
nano manual named pics/manual update Aug 2018 small JPEG selects/018-TripleConnectorSolder011000pxAnnotated.jpg
