Safecast/bGeigieNanoKit/nano manual named pics/manual update Aug 2018 small JPEG selects/019-TripleConnectorSolder021000pxAnnotated.jpg

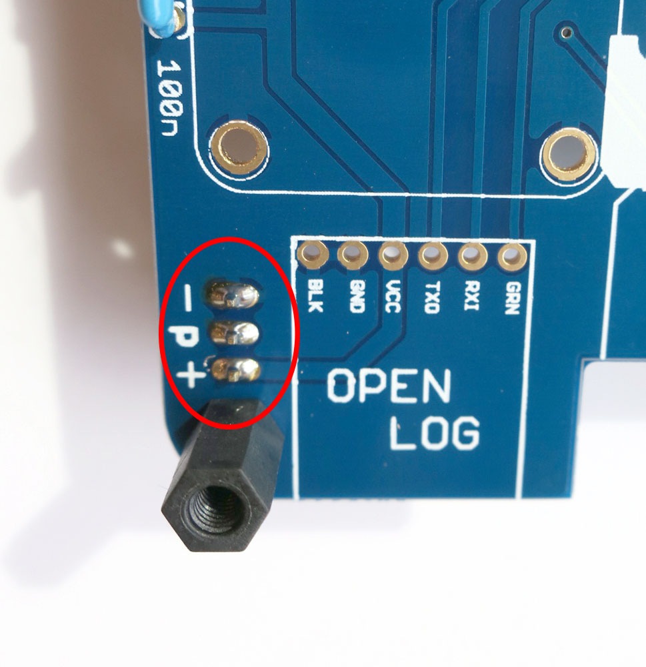
nano manual named pics/manual update Aug 2018 small JPEG selects/019-TripleConnectorSolder021000pxAnnotated.jpg
