Safecast/bGeigieNanoKit/nano manual named pics/manual update Aug 2018 small JPEG selects/021-OpenLogSpot1000pxAnnotated.jpg

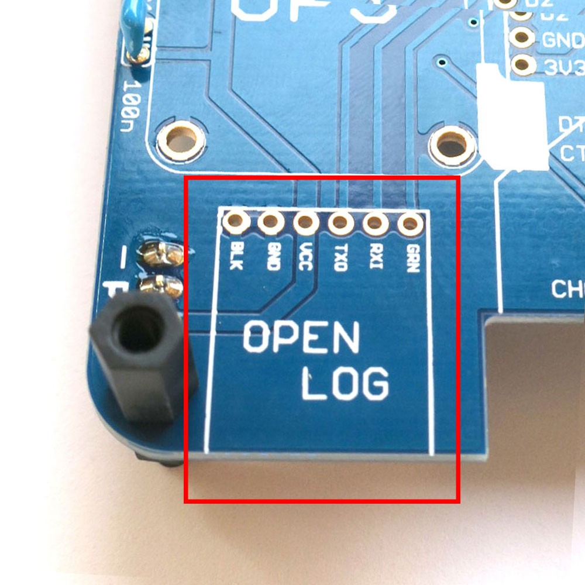
nano manual named pics/manual update Aug 2018 small JPEG selects/021-OpenLogSpot1000pxAnnotated.jpg
