Safecast/bGeigieNanoKit/nano manual named pics/manual update Aug 2018 small JPEG selects/023-OpenLogTape1000px.jpg

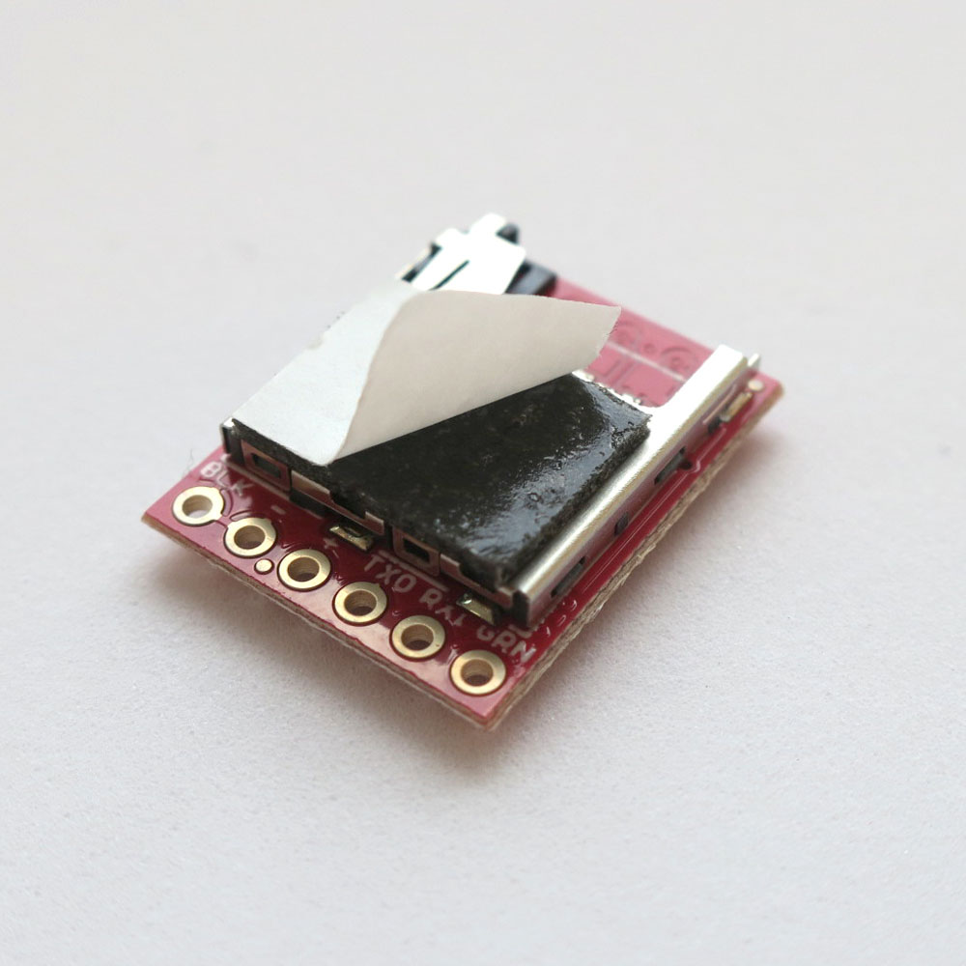
nano manual named pics/manual update Aug 2018 small JPEG selects/023-OpenLogTape1000px.jpg
