Safecast/bGeigieNanoKit/nano manual named pics/manual update Aug 2018 small JPEG selects/024-OpenLogHeaderIn1000pxAnnotated.jpg

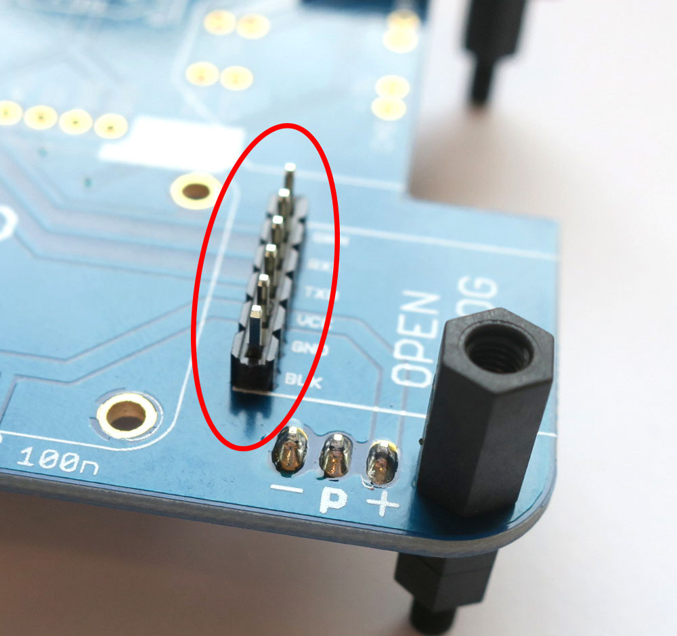
nano manual named pics/manual update Aug 2018 small JPEG selects/024-OpenLogHeaderIn1000pxAnnotated.jpg
