Safecast/bGeigieNanoKit/nano manual named pics/manual update Aug 2018 small JPEG selects/025-OpenLogSoldered1000px.jpg

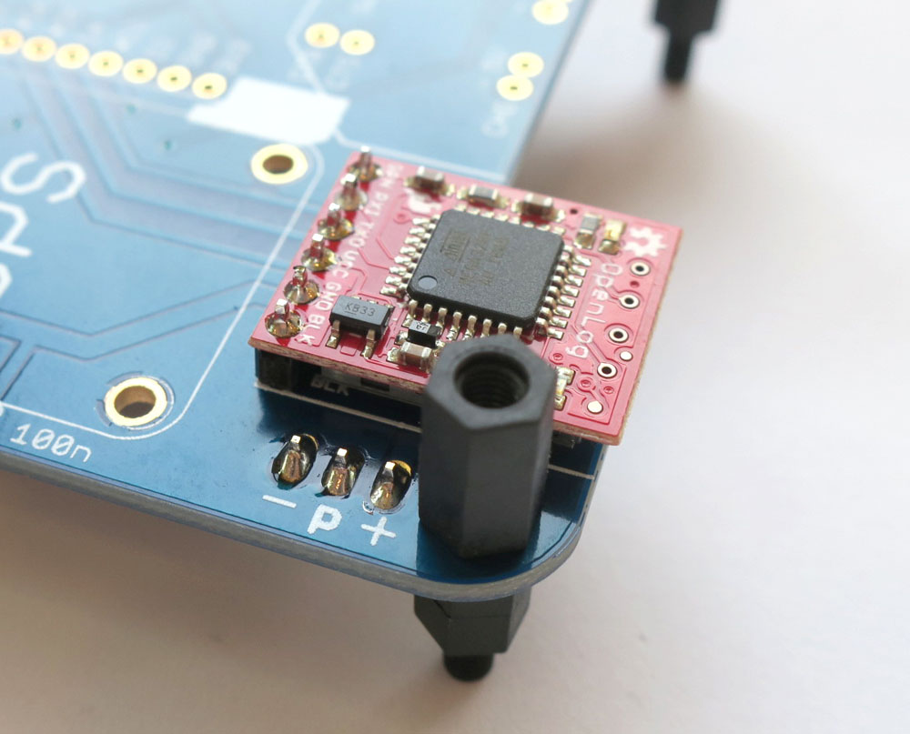
nano manual named pics/manual update Aug 2018 small JPEG selects/025-OpenLogSoldered1000px.jpg
