Safecast/bGeigieNanoKit/nano manual named pics/manual update Aug 2018 small JPEG selects/026-FIOwAngledHeader1000px.jpg

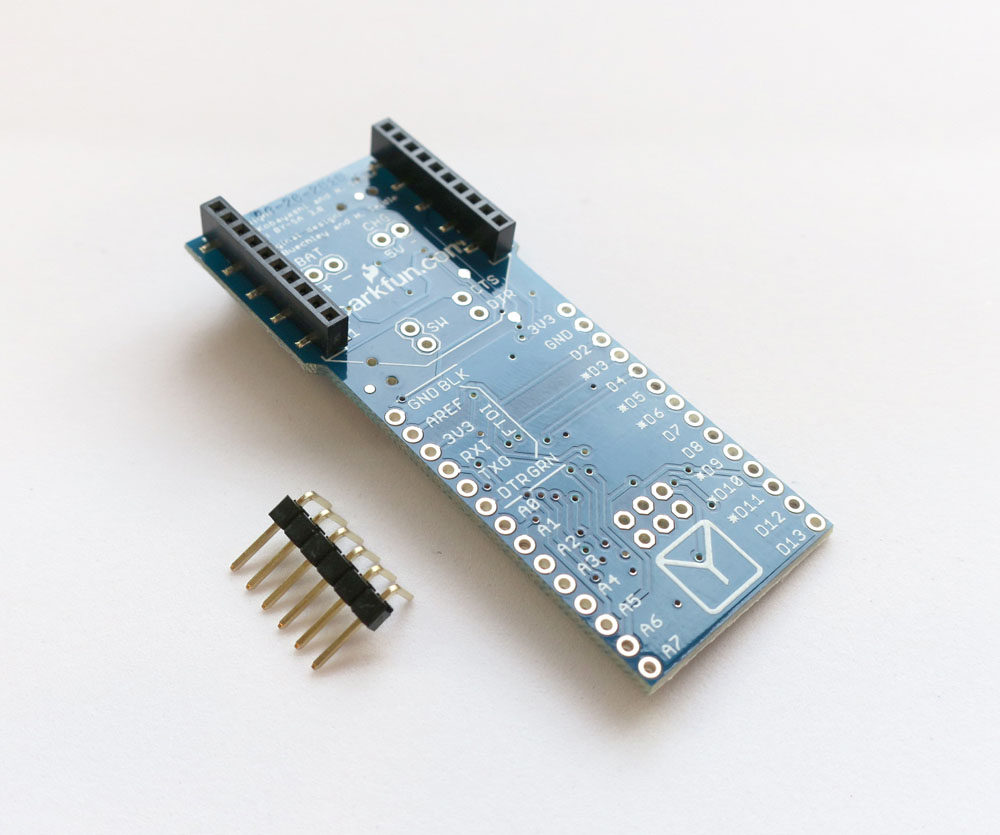
nano manual named pics/manual update Aug 2018 small JPEG selects/026-FIOwAngledHeader1000px.jpg
