Safecast/bGeigieNanoKit/nano manual named pics/manual update Aug 2018 small JPEG selects/028-FIOheadersIn1000pxAnnotated.jpg

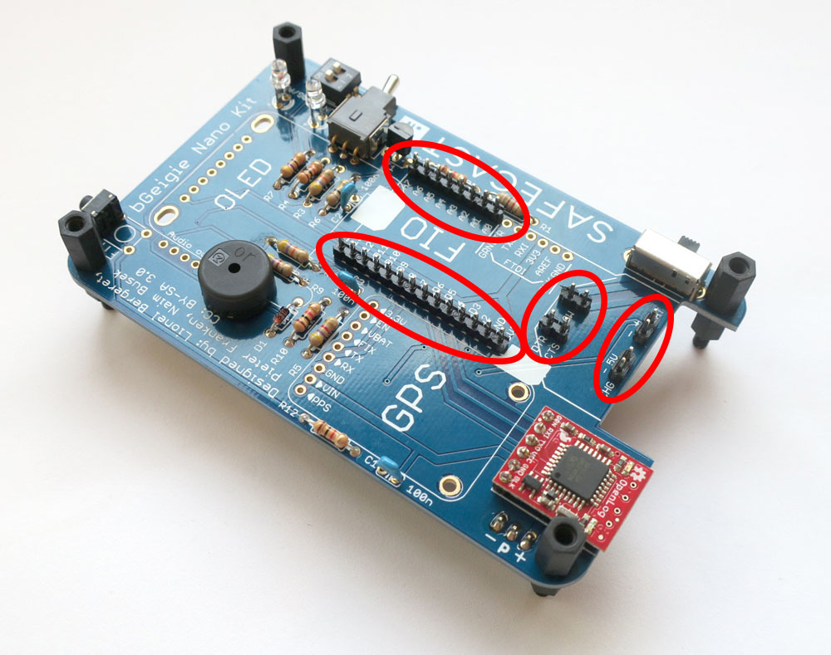
nano manual named pics/manual update Aug 2018 small JPEG selects/028-FIOheadersIn1000pxAnnotated.jpg
