Safecast/bGeigieNanoKit/nano manual named pics/manual update Aug 2018 small JPEG selects/029-FIOunsoldered1000px.jpg

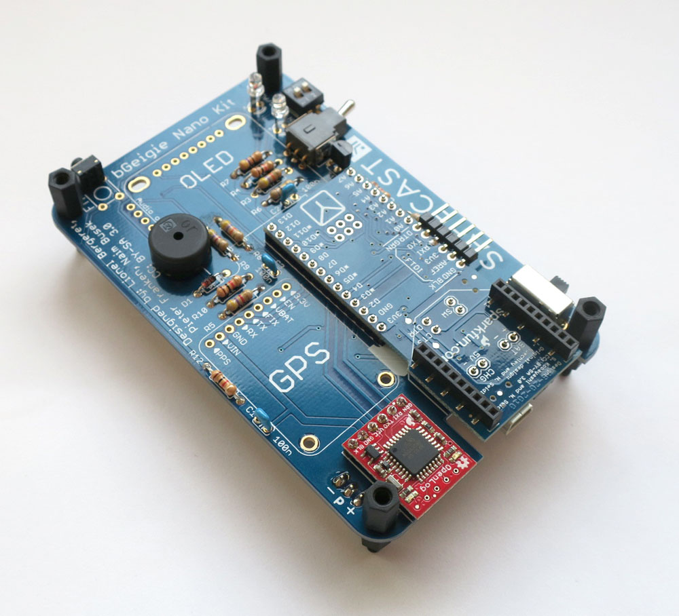
nano manual named pics/manual update Aug 2018 small JPEG selects/029-FIOunsoldered1000px.jpg
