Safecast/bGeigieNanoKit/nano manual named pics/manual update Aug 2018 small JPEG selects/035-GPSinstalled1000pxAnnotated.jpg

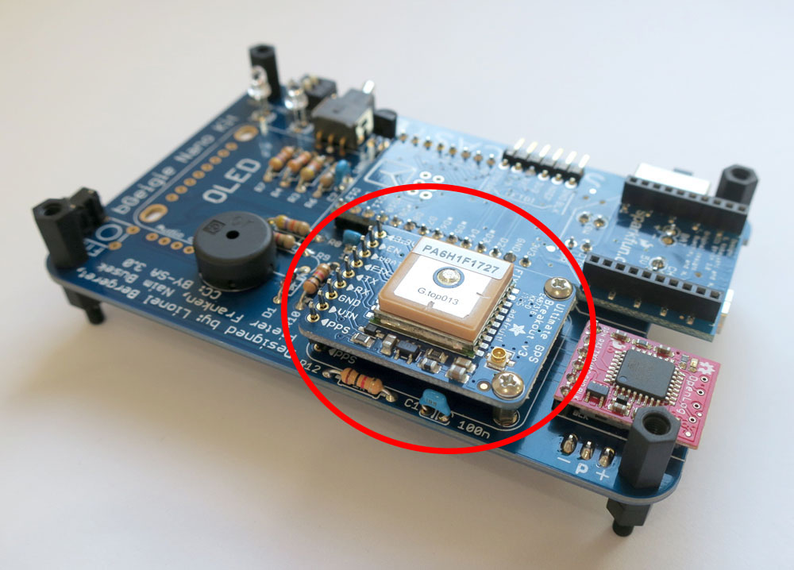
nano manual named pics/manual update Aug 2018 small JPEG selects/035-GPSinstalled1000pxAnnotated.jpg
