Safecast/bGeigieNanoKit/nano manual named pics/manual update Aug 2018 small JPEG selects/041-PowerOnSuccess1000px.jpg

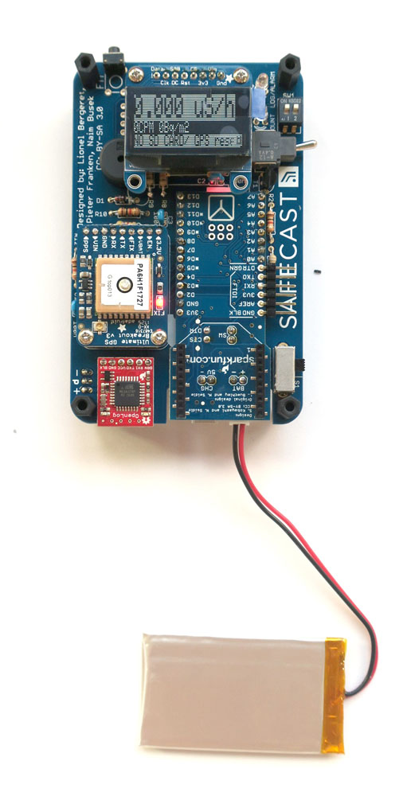
nano manual named pics/manual update Aug 2018 small JPEG selects/041-PowerOnSuccess1000px.jpg
