Safecast/bGeigieNanoKit/nano manual named pics/manual update Aug 2018 small JPEG selects/045-BatteryTape011000px.jpg

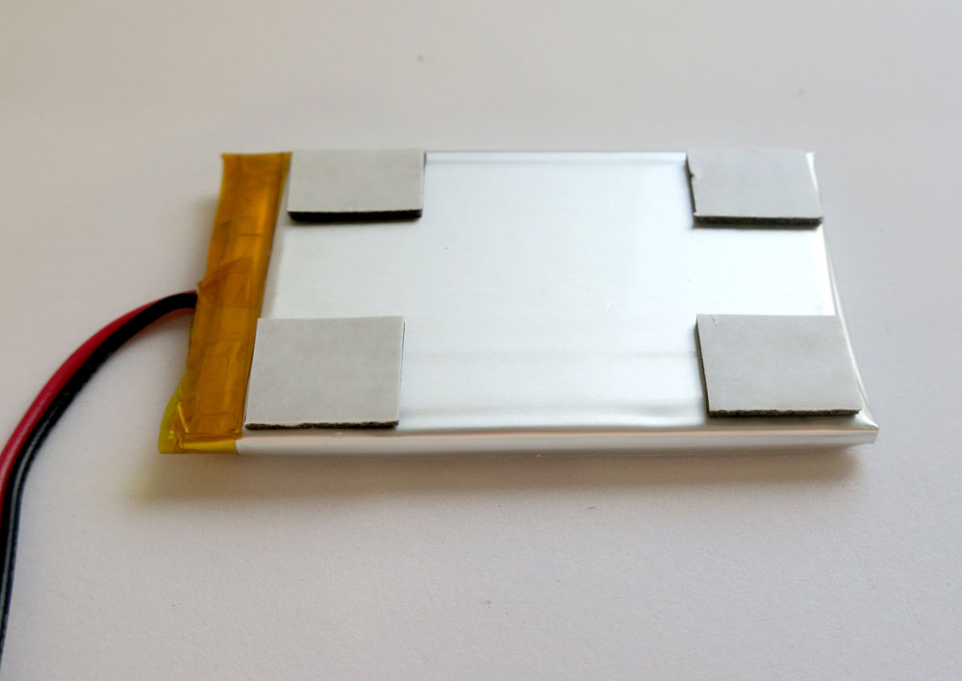
nano manual named pics/manual update Aug 2018 small JPEG selects/045-BatteryTape011000px.jpg
