Safecast/bGeigieNanoKit/nano manual named pics/manual update Aug 2018 small JPEG selects/045-BatteryTapePlastic011000pxAnnotated.jpg

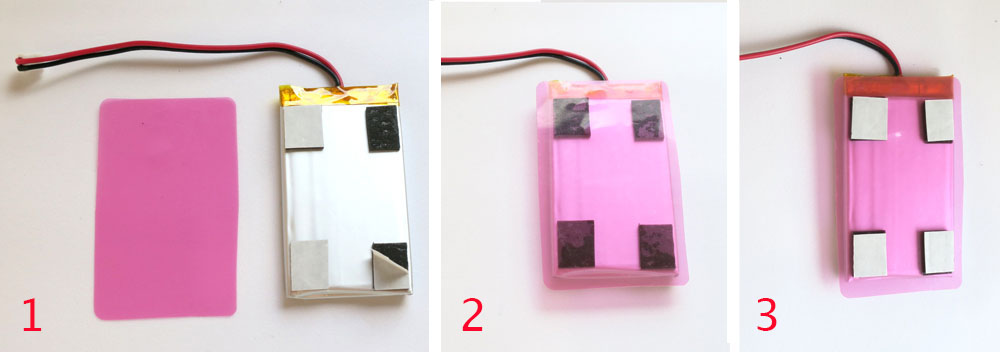
nano manual named pics/manual update Aug 2018 small JPEG selects/045-BatteryTapePlastic011000pxAnnotated.jpg
