Safecast/bGeigieNanoKit/nano manual named pics/manual update Aug 2018 small JPEG selects/049-iRoverRear1000pxAnnotated.jpg

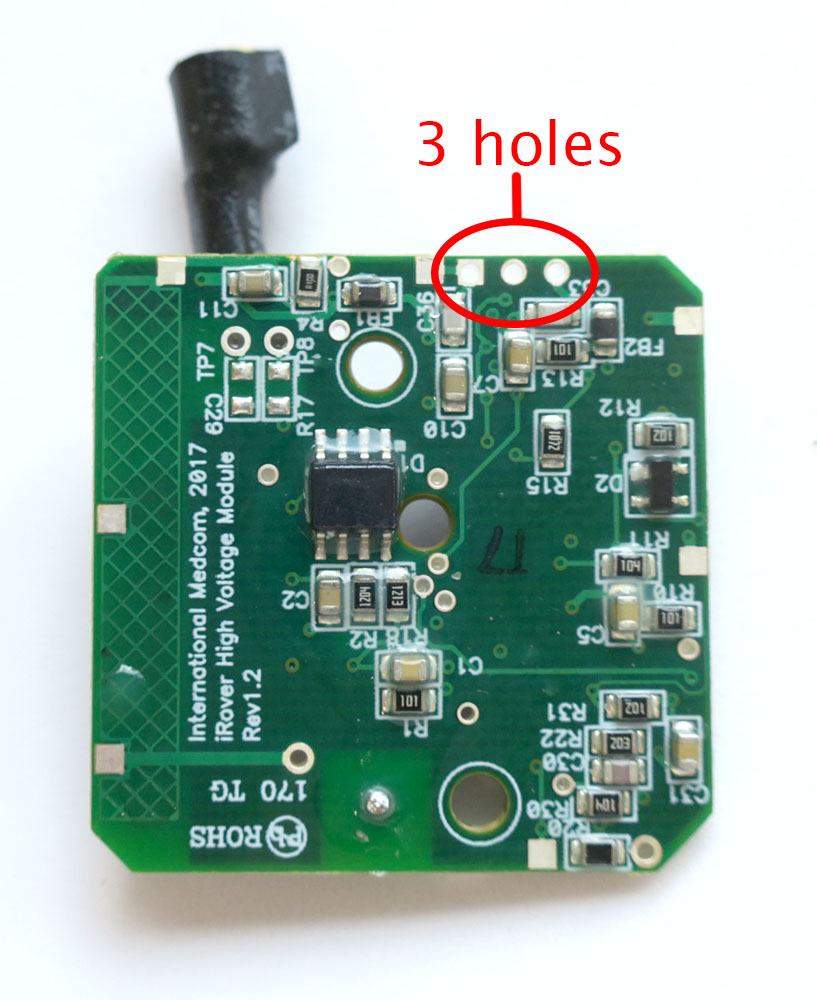
nano manual named pics/manual update Aug 2018 small JPEG selects/049-iRoverRear1000pxAnnotated.jpg
