Safecast/bGeigieNanoKit/nano manual named pics/manual update Aug 2018 small JPEG selects/052-MiddlePlateStandoffs1000pxAnnotatedv02.jpg

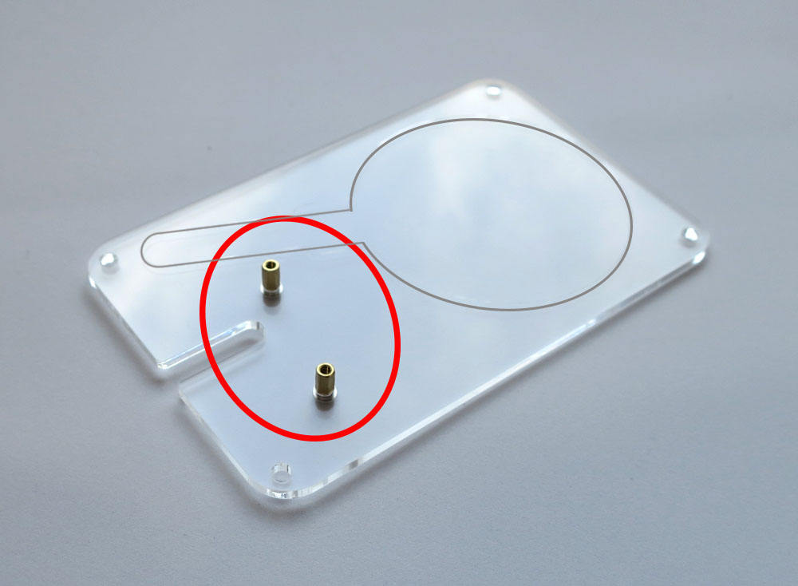
nano manual named pics/manual update Aug 2018 small JPEG selects/052-MiddlePlateStandoffs1000pxAnnotatedv02.jpg
