Safecast/bGeigieNanoKit/nano manual named pics/manual update Aug 2018 small JPEG selects/055-3wireConnector1000pxAnnotated.jpg

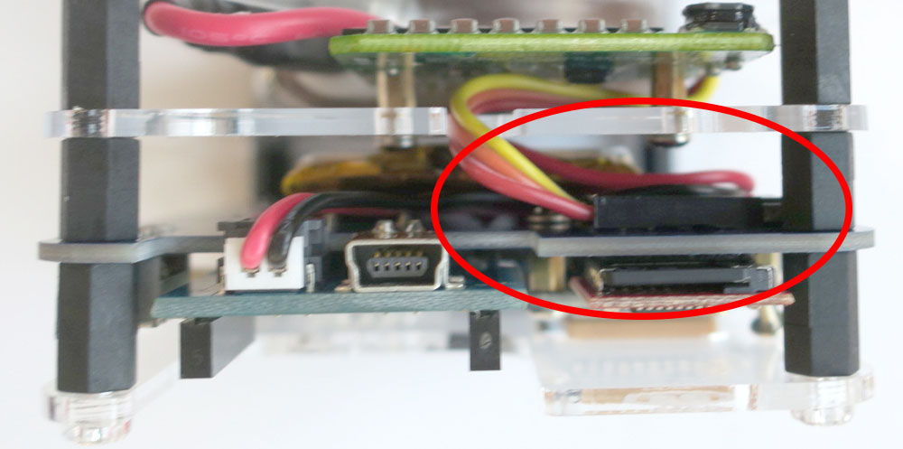
nano manual named pics/manual update Aug 2018 small JPEG selects/055-3wireConnector1000pxAnnotated.jpg
