Safecast/bGeigieNanoKit/nano manual named pics/manual update Aug 2018 small JPEG selects/056-SensorTape1000px.jpg

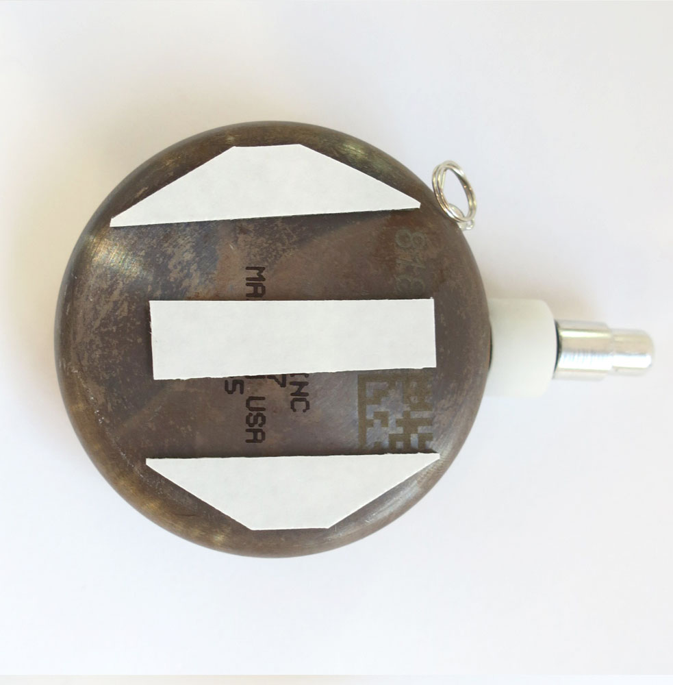
nano manual named pics/manual update Aug 2018 small JPEG selects/056-SensorTape1000px.jpg
