Safecast/bGeigieNanoKit/nano manual named pics/manual update Aug 2018 small JPEG selects/063-StackImage011000px.jpg

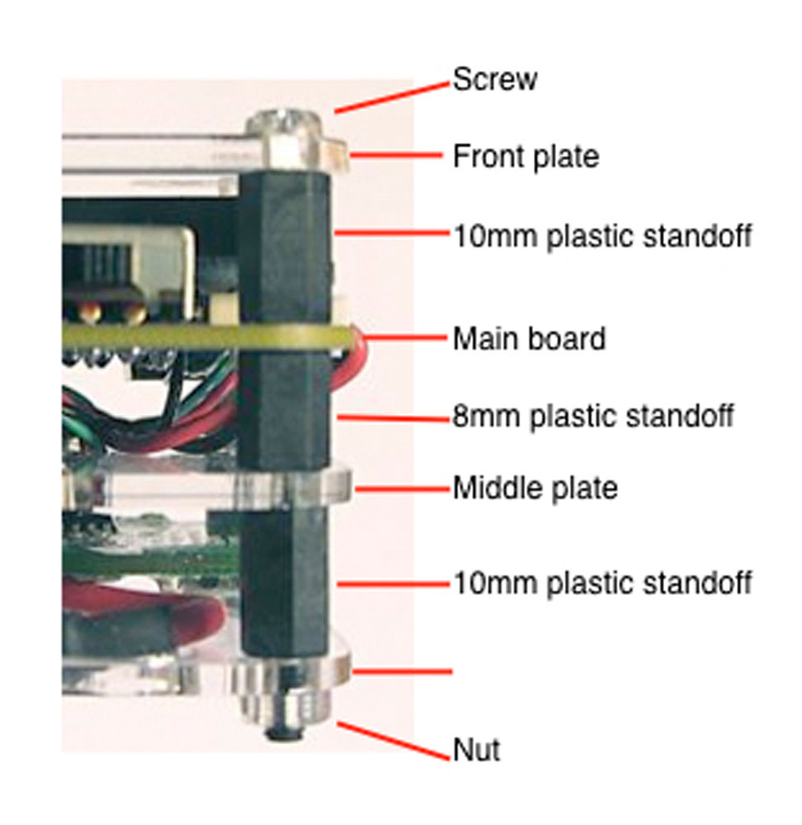
nano manual named pics/manual update Aug 2018 small JPEG selects/063-StackImage011000px.jpg
