Safecast/bGeigieNanoKit/nano manual named pics/manual update Aug 2018 small JPEG selects/066-NanoTop1000px.jpg

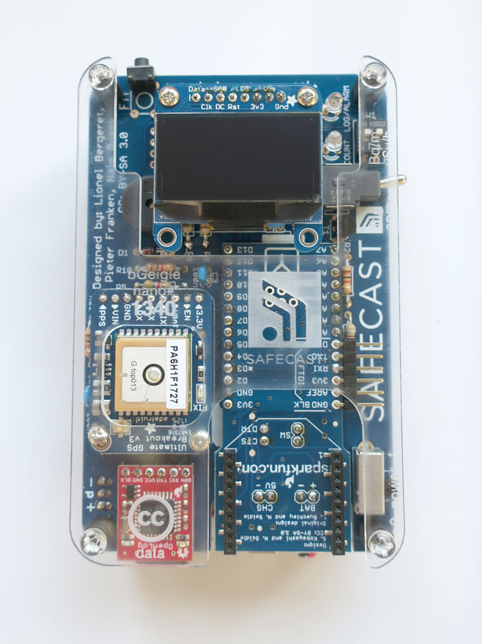
nano manual named pics/manual update Aug 2018 small JPEG selects/066-NanoTop1000px.jpg
