Safecast/bGeigieNanoKit/nano manual named pics/manual update Aug 2018 small JPEG selects/067-NanoBottom1000px.jpg

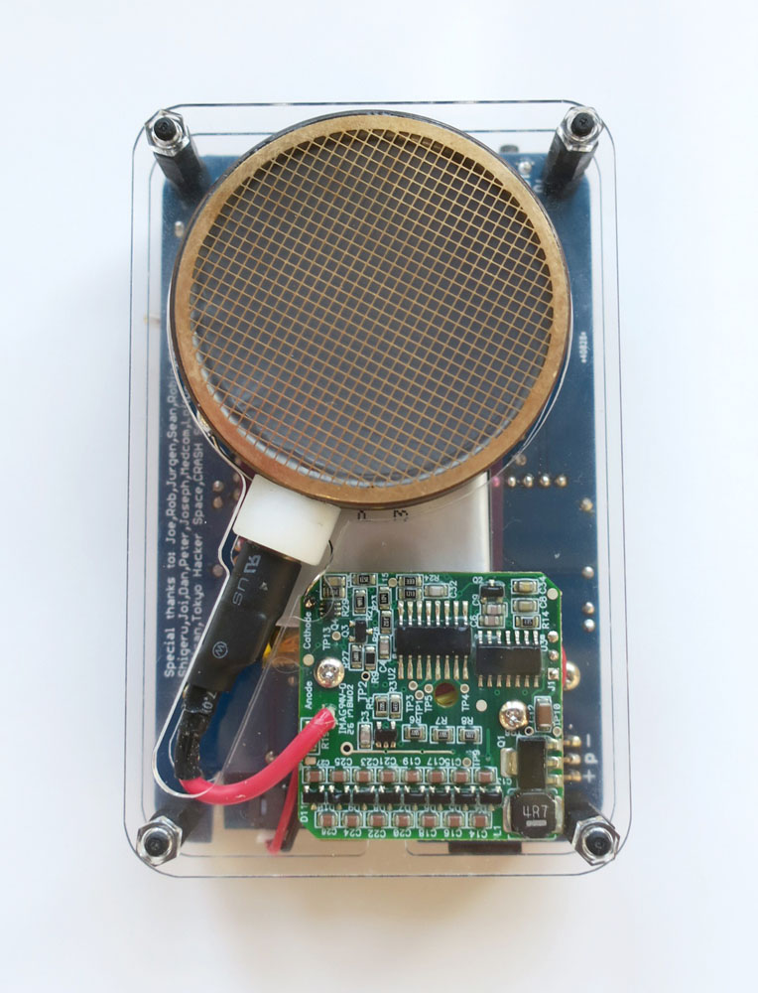
nano manual named pics/manual update Aug 2018 small JPEG selects/067-NanoBottom1000px.jpg
