Safecast/bGeigieNanoKit/nano manual named pics/manual update Aug 2018 small JPEG selects/072-CaseLabel011000px.jpg

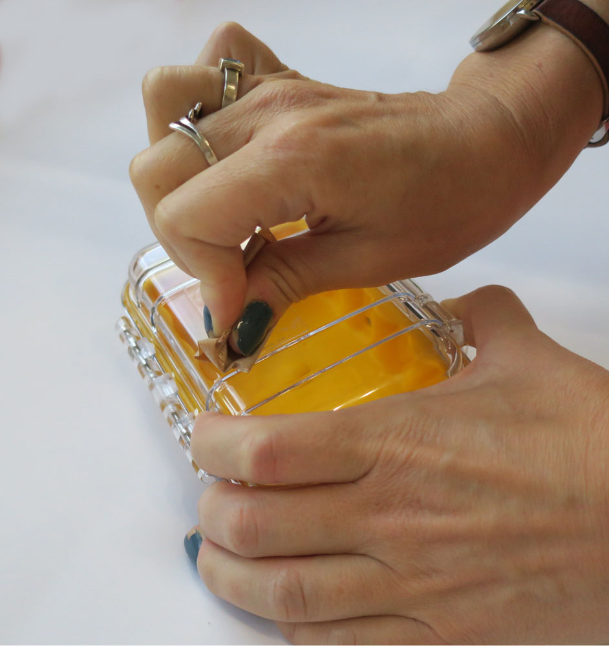
nano manual named pics/manual update Aug 2018 small JPEG selects/072-CaseLabel011000px.jpg
