Safecast/bGeigieNanoKit/nano manual named pics/manual update Aug 2018 small JPEG selects/077 three_plates1000pxAnnotated[new].jpg

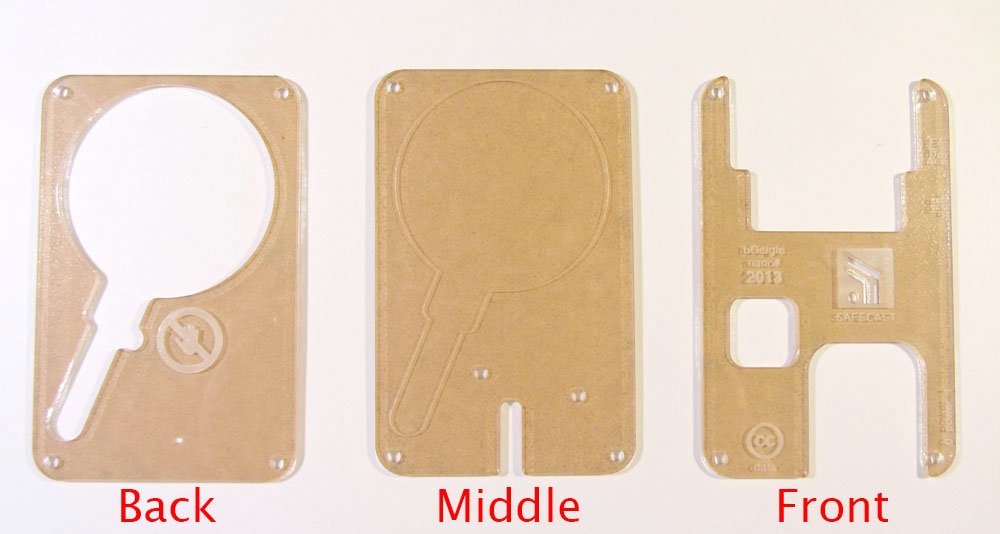
nano manual named pics/manual update Aug 2018 small JPEG selects/077 three_plates1000pxAnnotated[new].jpg
