Safecast/bGeigieNanoKit/nano manual named pics/nailpolishtrick.jpg

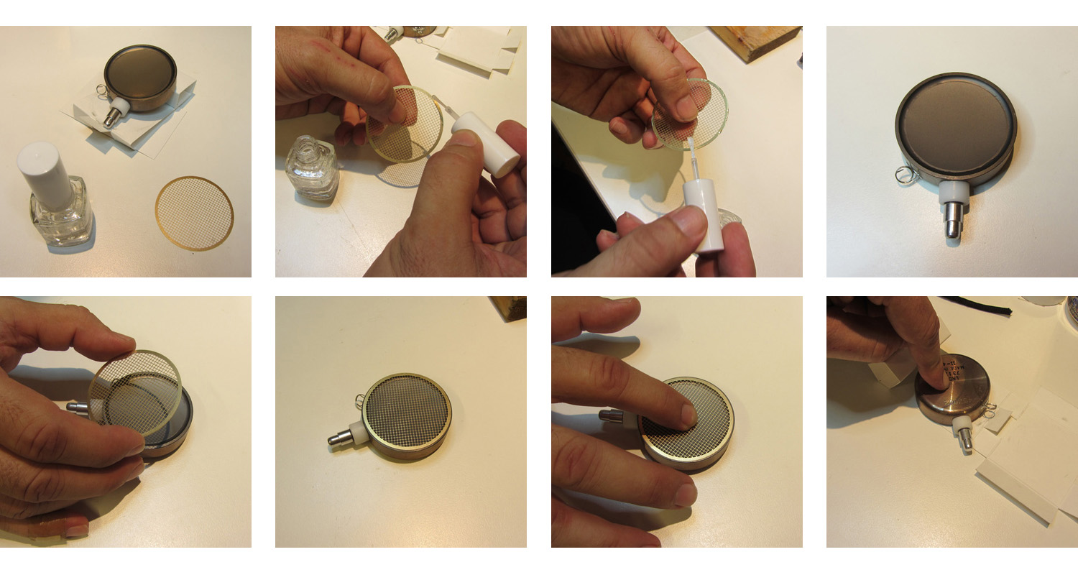
nano manual named pics/nailpolishtrick.jpg
