Safecast/bGeigieNanoKit/nano manual named pics/openlog_tape.jpg

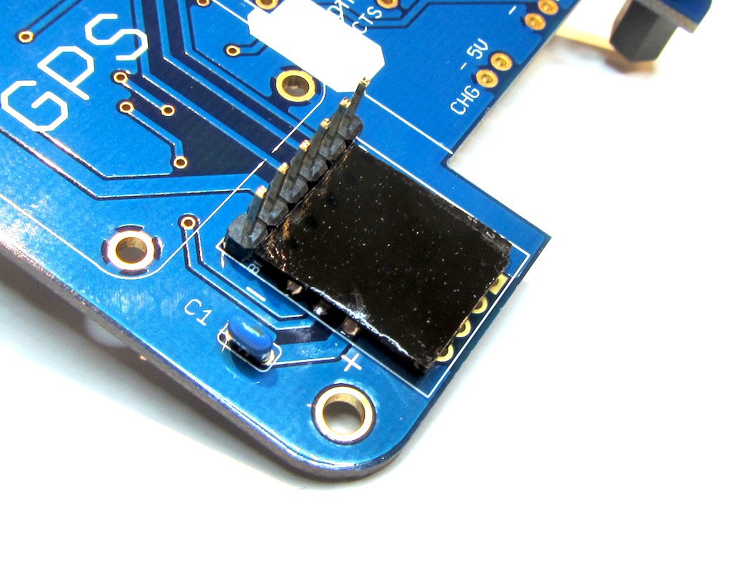
nano manual named pics/openlog_tape.jpg
