Safecast/bGeigieNanoKit/nano manual named pics/overviewpics/bGeigie Nano manual v5.3big_Page_04_Image_0011.jpg

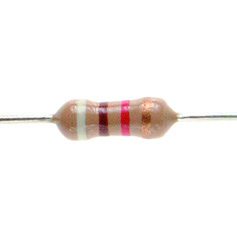
nano manual named pics/overviewpics/bGeigie Nano manual v5.3big_Page_04_Image_0011.jpg
