Safecast/bGeigieNanoKit/nano manual named pics/overviewpics/bGeigie Nano manual v5.3big_Page_07_Image_0001.jpg

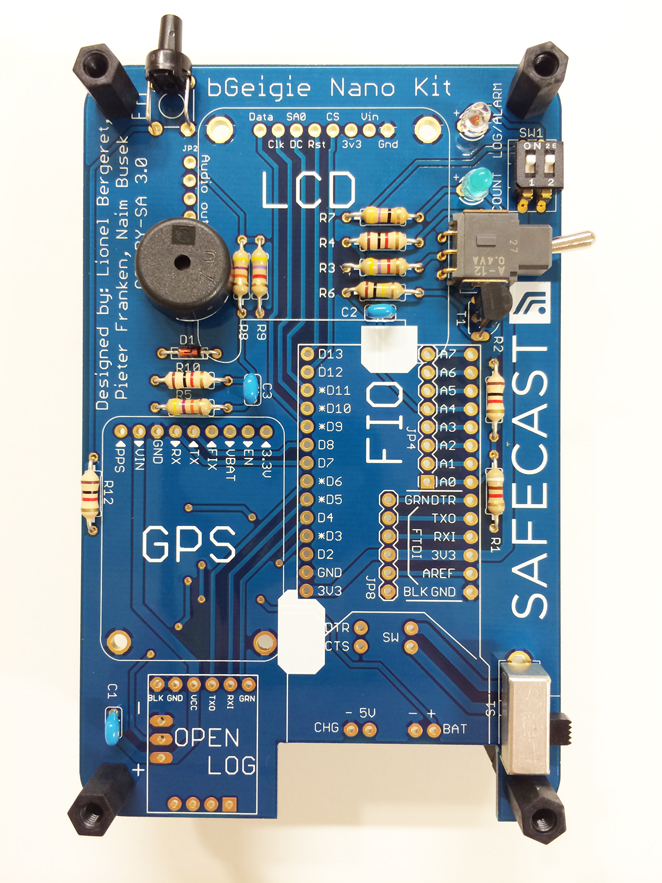
nano manual named pics/overviewpics/bGeigie Nano manual v5.3big_Page_07_Image_0001.jpg
