Safecast/bGeigieNanoKit/nano manual named pics/overviewpics/bGeigie Nano manual v5.3big_Page_10_Image_0002.jpg

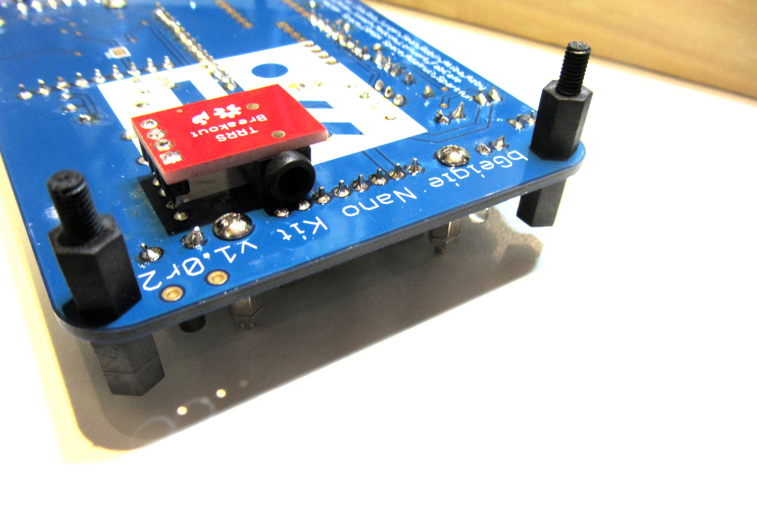
nano manual named pics/overviewpics/bGeigie Nano manual v5.3big_Page_10_Image_0002.jpg
