Safecast/bGeigieNanoKit/nano manual named pics/overviewpics/bGeigie Nano manual v5.3big_Page_11_Image_0006.jpg

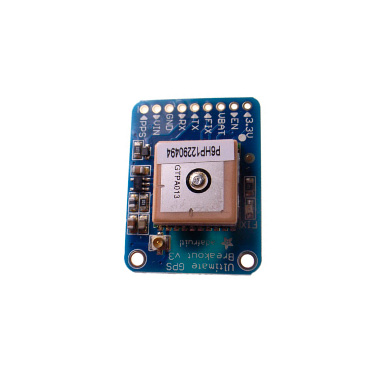
nano manual named pics/overviewpics/bGeigie Nano manual v5.3big_Page_11_Image_0006.jpg
