Safecast/bGeigieNanoKit/nano manual named pics/sensor.jpg

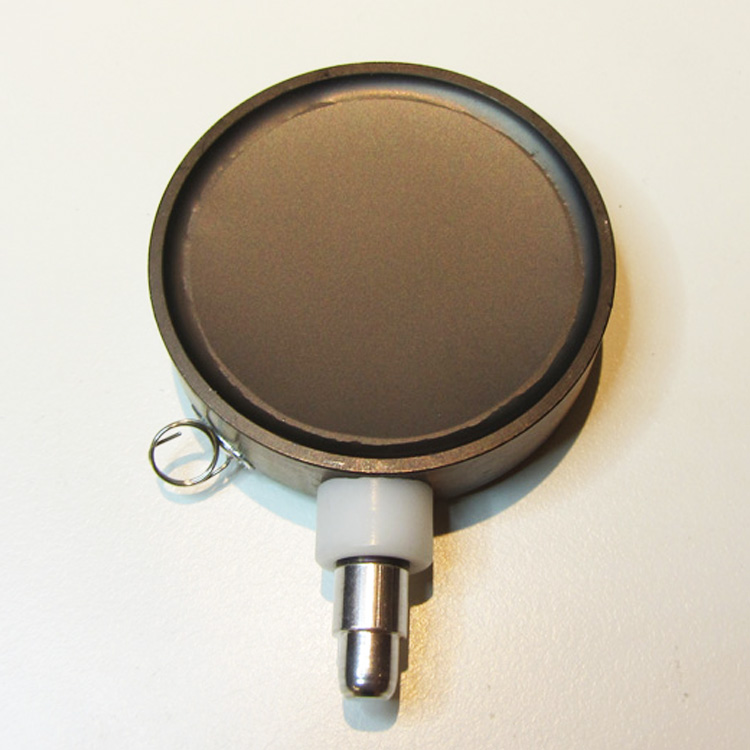
nano manual named pics/sensor.jpg
