Safecast/bGeigieNanoKit/nano manual named pics/sensor_box.jpg

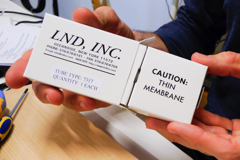
nano manual named pics/sensor_box.jpg
