Safecast/bGeigieNanoKit/nano manual named pics/sensor_cover.jpg

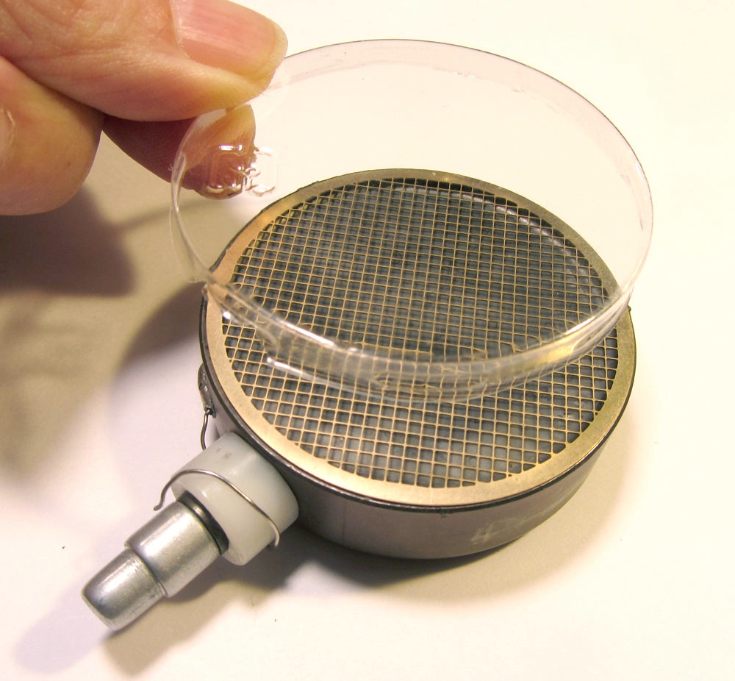
nano manual named pics/sensor_cover.jpg
