Safecast/bGeigieNanoKit/nano manual named pics/sensor_placement.jpg

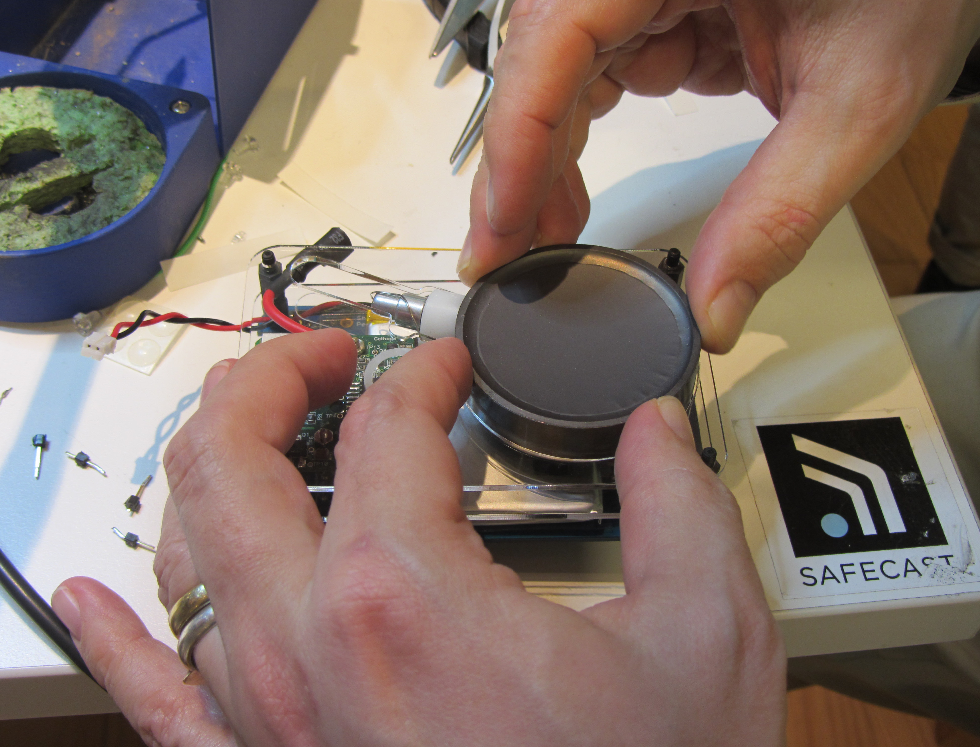
nano manual named pics/sensor_placement.jpg
