Safecast/bGeigieNanoKit/nano manual named pics/soldering_sensor_ground.jpg

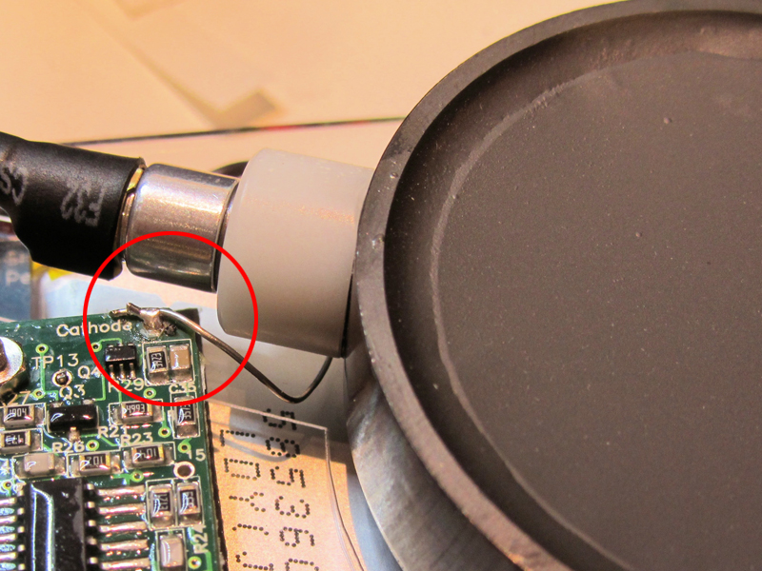
nano manual named pics/soldering_sensor_ground.jpg
