Safecast/bGeigieNanoKit/nano manual named pics/spacers.jpg

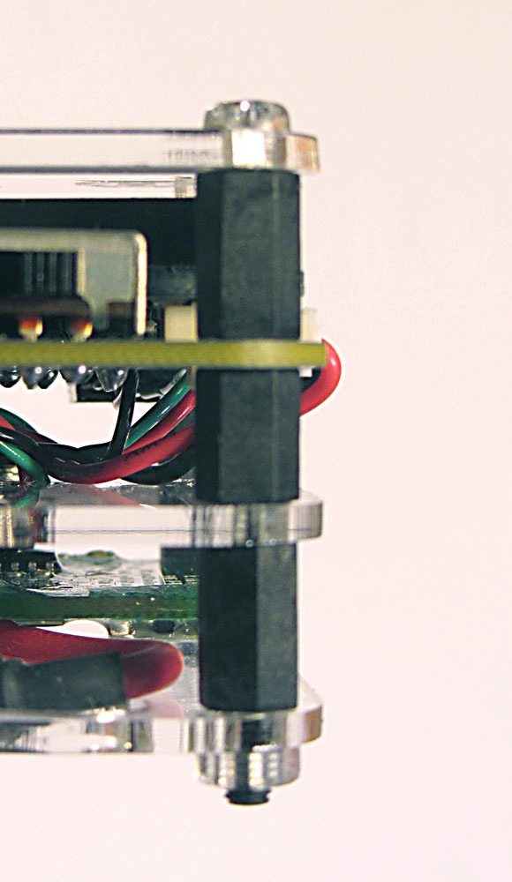
nano manual named pics/spacers.jpg
