Safecast/bGeigieNanoKit/nano manual named pics/spacers_and_nut.jpg

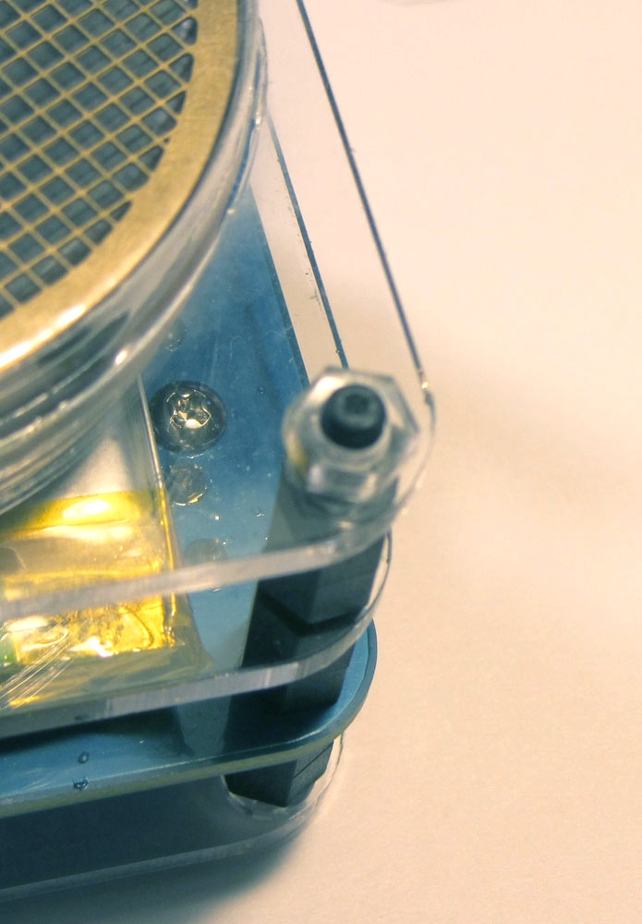
nano manual named pics/spacers_and_nut.jpg
