Safecast/bGeigieNanoKit/nano manual named pics/spacers_and_screws.jpg

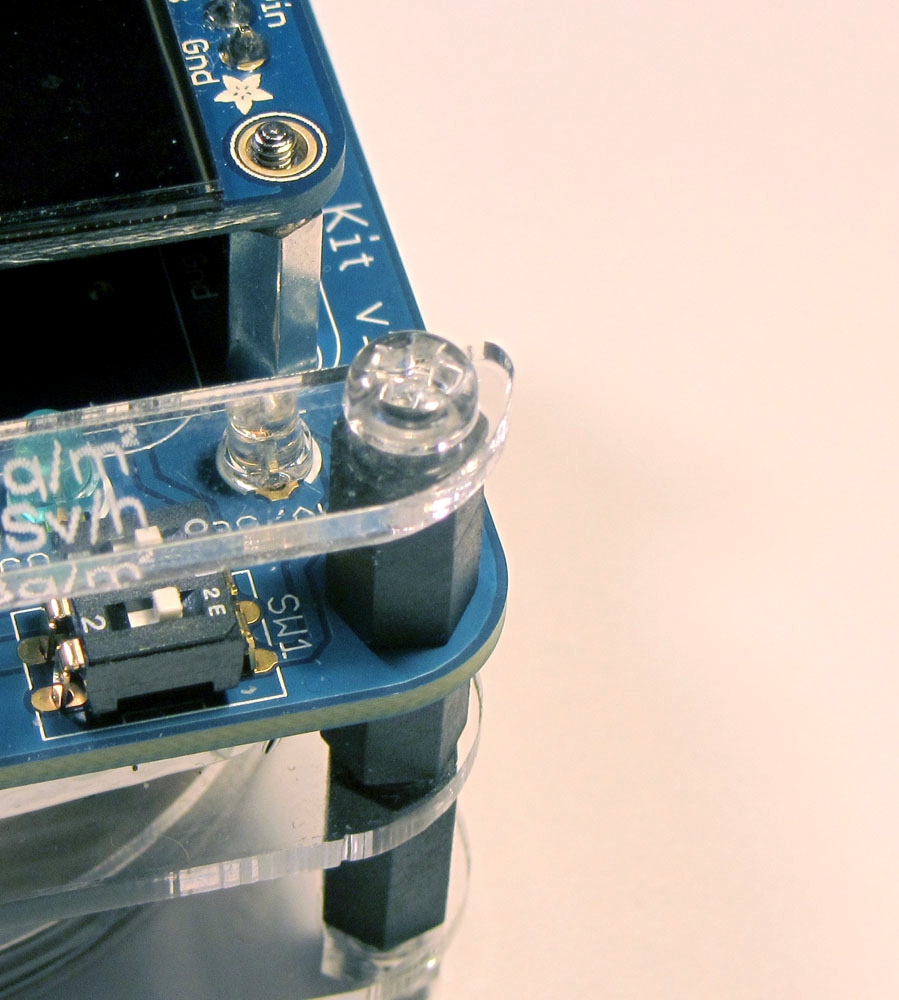
nano manual named pics/spacers_and_screws.jpg
