Safecast/bGeigieNanoKit/nano manual named pics/three_plates.jpg

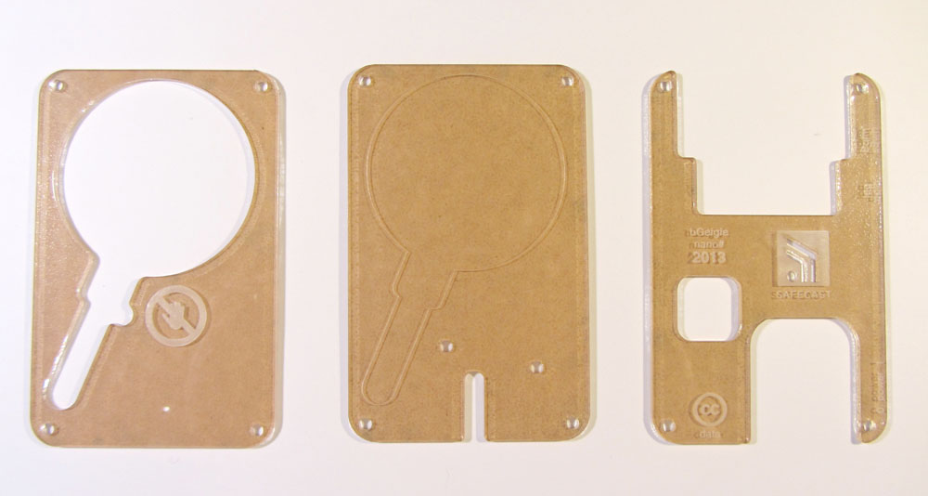
nano manual named pics/three_plates.jpg
