Safecast/bGeigieNanoKit/nano manual named pics/v1.0r2_page1.jpg

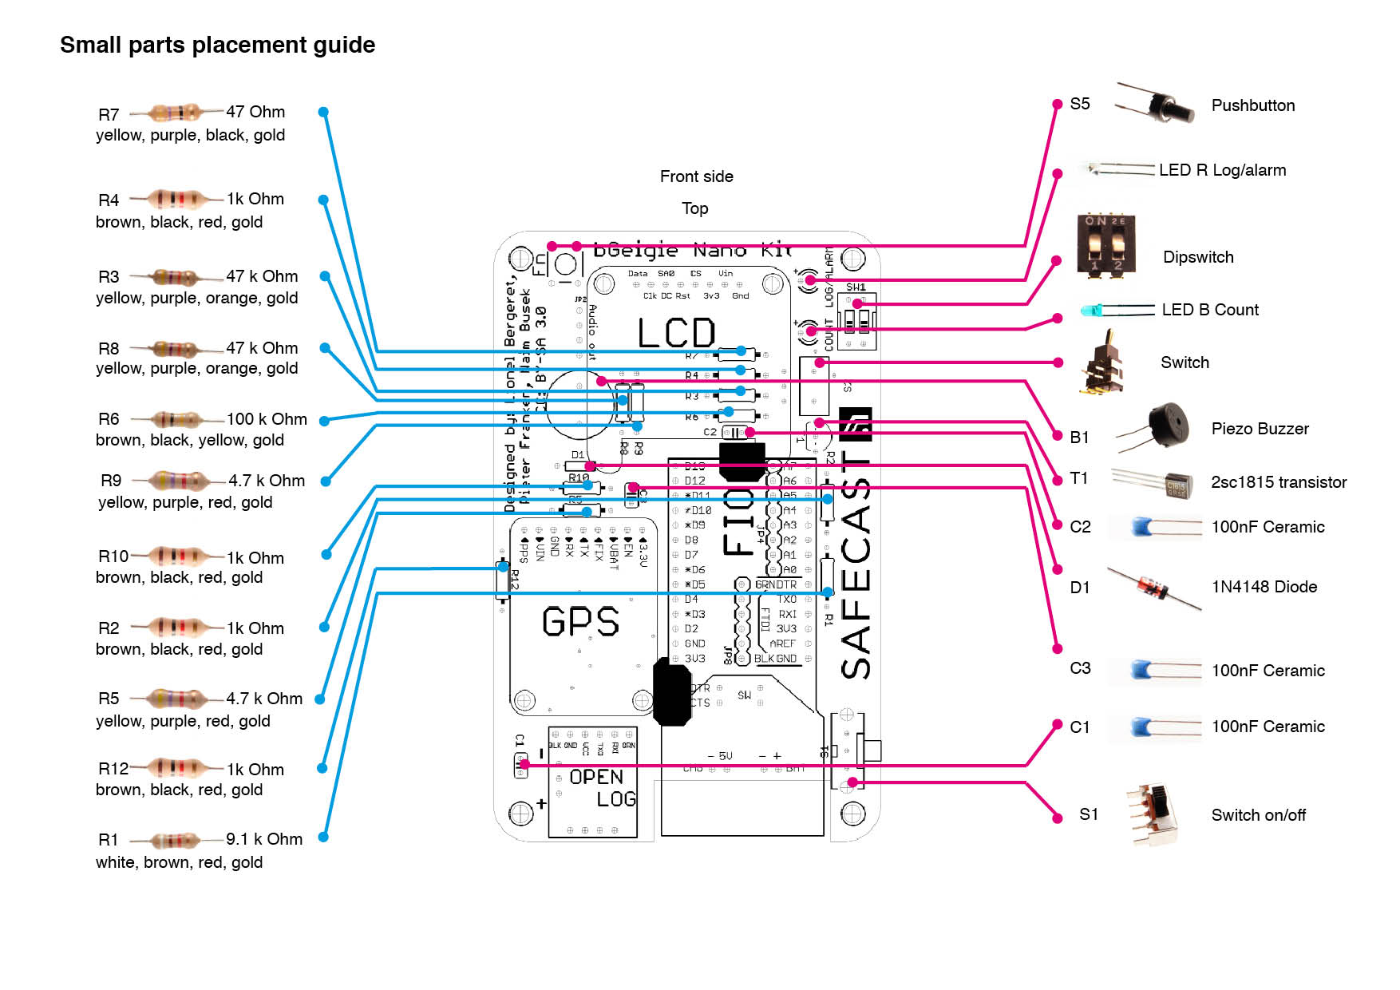
nano manual named pics/v1.0r2_page1.jpg
