Safecast/bGeigieNanoKit/nano manual named pics/v1.0r2_page12.jpg

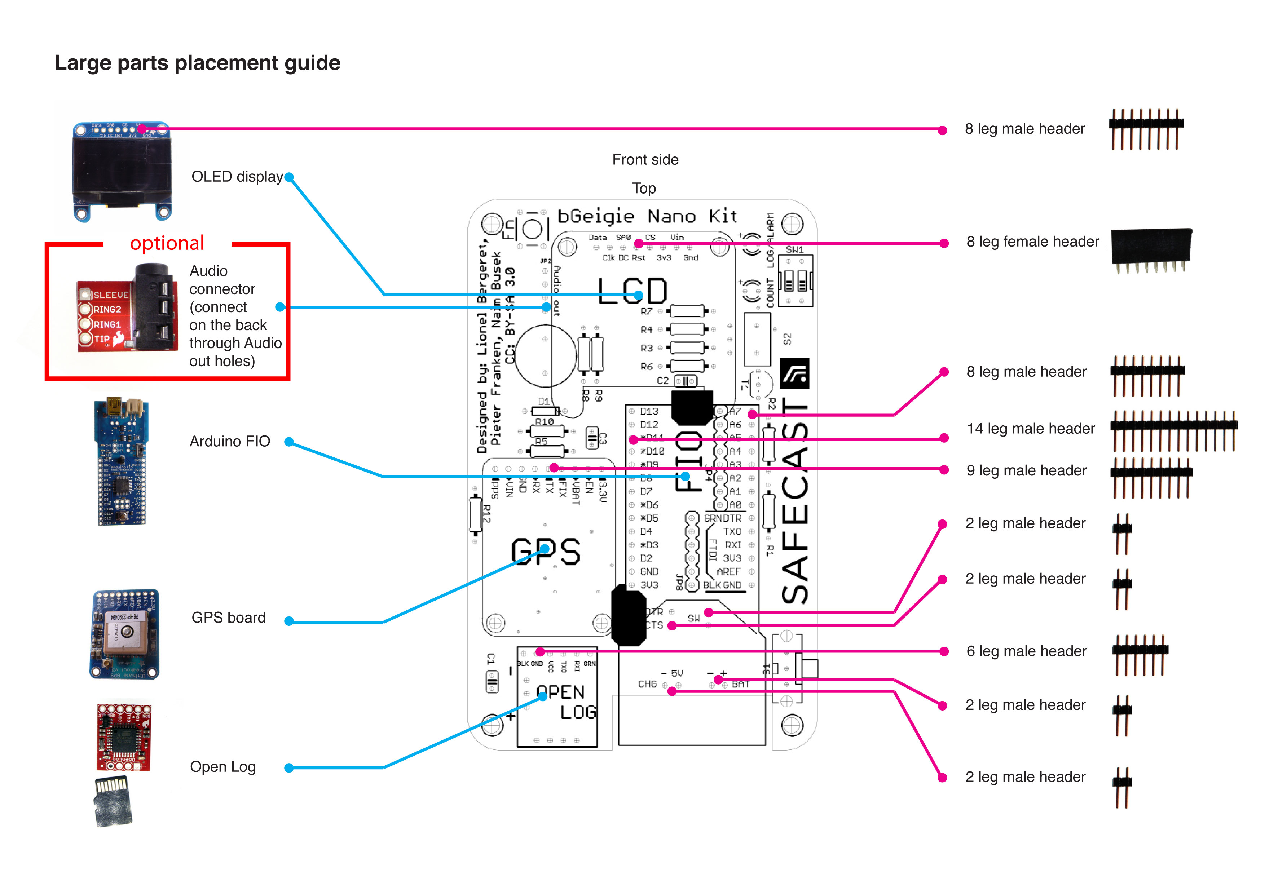
nano manual named pics/v1.0r2_page12.jpg
